mkellsy/rpi-case-model/CULTS3D/RPI-1.PNG

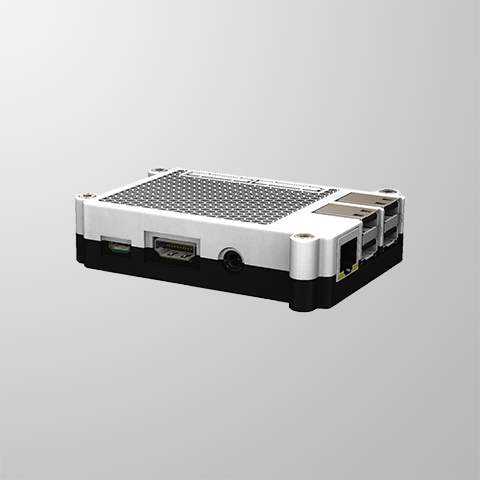
CULTS3D/RPI-1.PNG
