mkellsy/rpi-case-model/CULTS3D/RPI-2.PNG

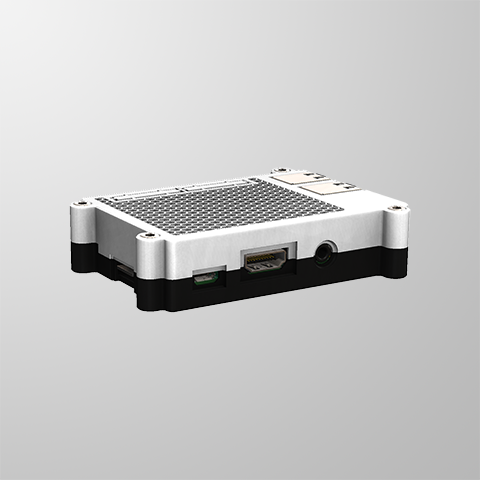
CULTS3D/RPI-2.PNG
