mkellsy/rpi-case-model/CULTS3D/RPI-3.PNG

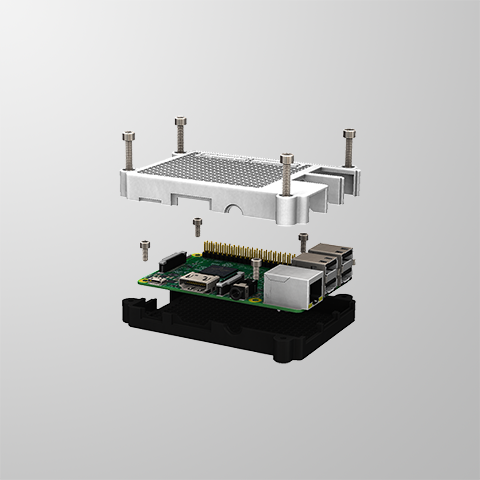
CULTS3D/RPI-3.PNG
