mkellsy/rpi-case-model/CULTS3D/RPI-4.PNG

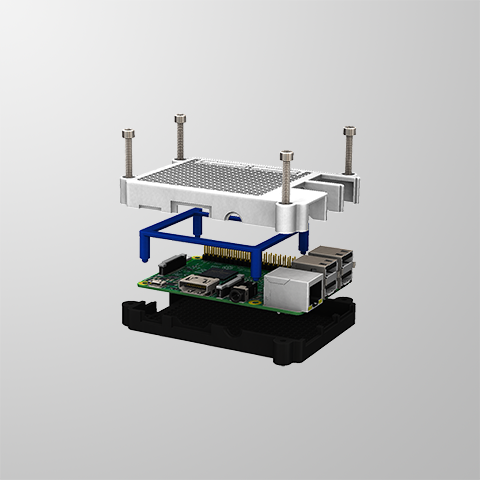
CULTS3D/RPI-4.PNG
