mkellsy/rpi-case-model/CULTS3D/RPI-5.PNG

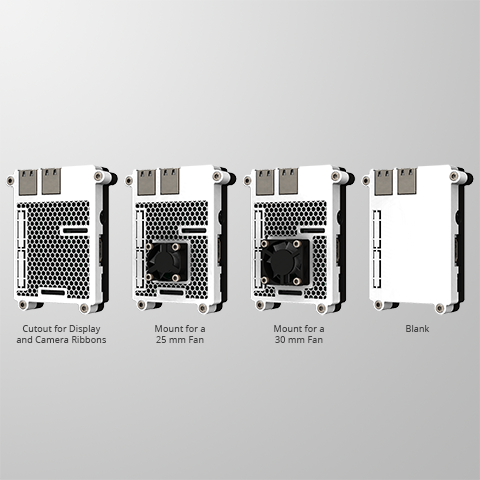
CULTS3D/RPI-5.PNG
