mkellsy/rpi-case-model/CULTS3D/RPI-6.PNG

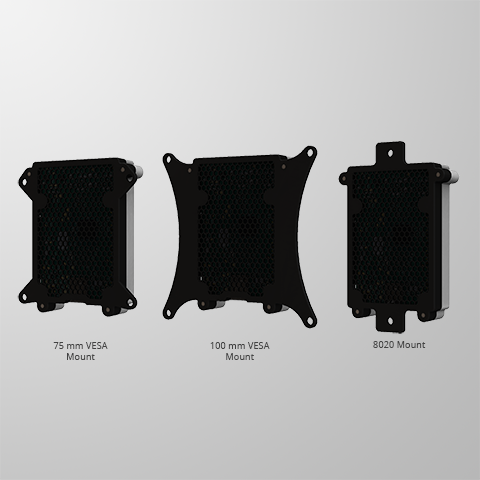
CULTS3D/RPI-6.PNG
