mkellsy/rpi-case-model/CULTS3D/RTS-1.PNG

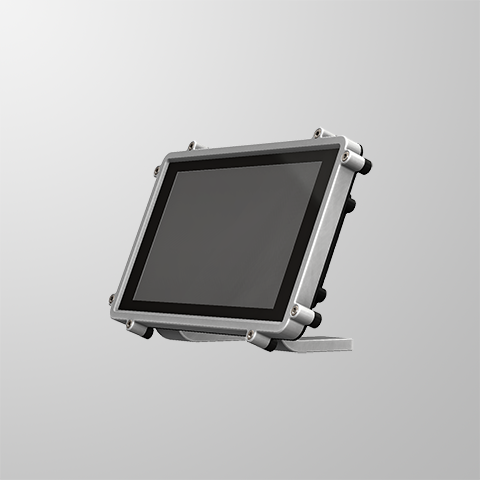
CULTS3D/RTS-1.PNG
