mkellsy/rpi-case-model/CULTS3D/RTS-2.PNG

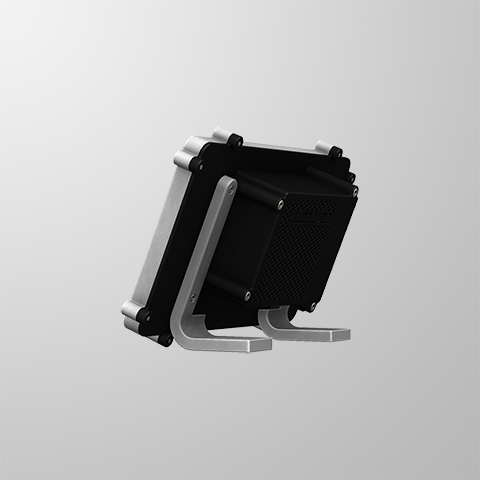
CULTS3D/RTS-2.PNG
