mkellsy/rpi-case-model/CULTS3D/RTS-3.PNG

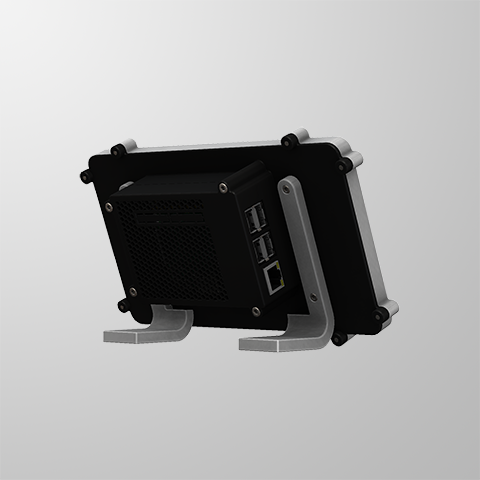
CULTS3D/RTS-3.PNG
