mkellsy/rpi-case-model/CULTS3D/RTS-4.PNG

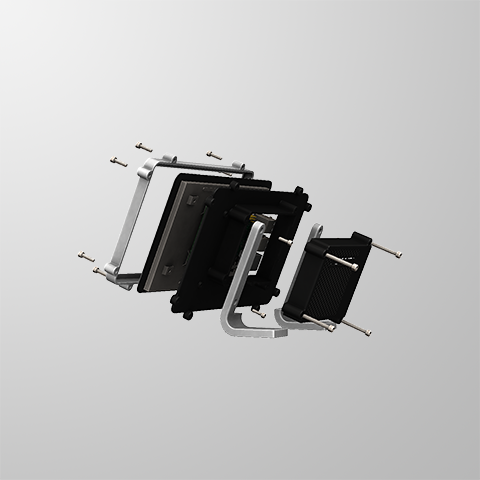
CULTS3D/RTS-4.PNG
