mkellsy/rpi-case-model/CULTS3D/RTS-5.PNG

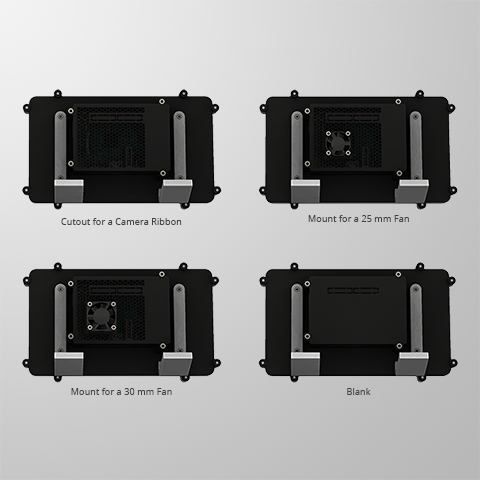
CULTS3D/RTS-5.PNG
