mkellsy/rpi-case-model/RENDERINGS/RPI3-1.JPG

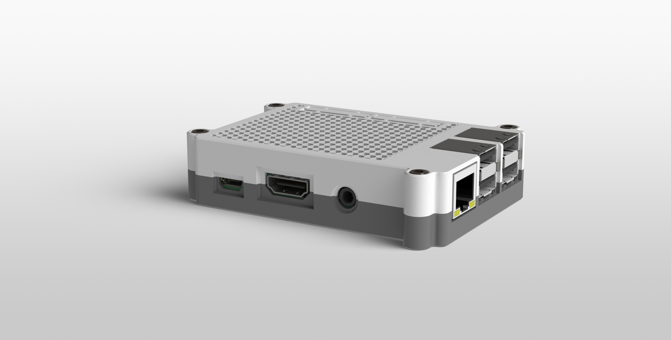
RENDERINGS/RPI3-1.JPG
