mkellsy/rpi-case-model/RENDERINGS/RPI3-2.JPG

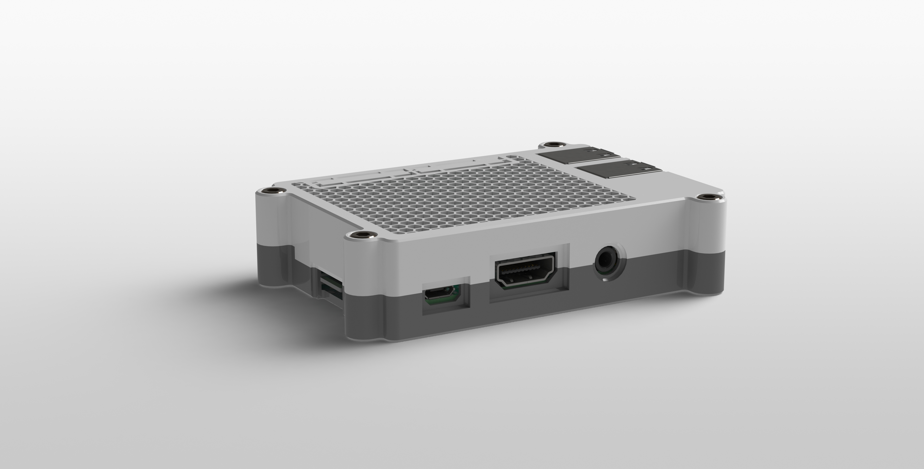
RENDERINGS/RPI3-2.JPG
