mkellsy/rpi-case-model/RENDERINGS/RPI3-3.JPG

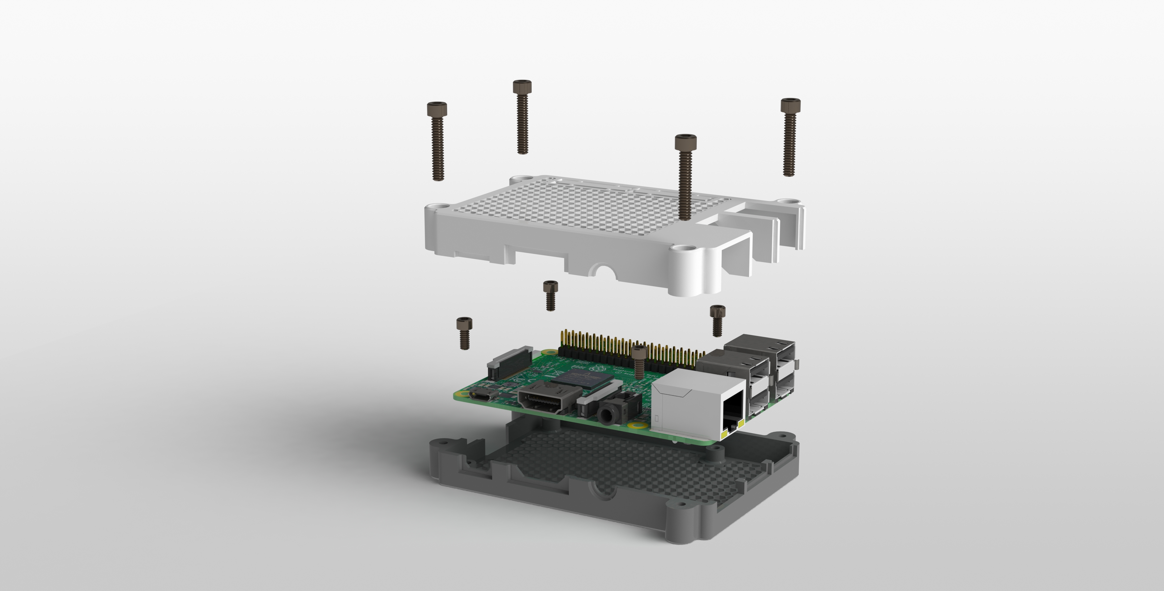
RENDERINGS/RPI3-3.JPG
