mkellsy/rpi-case-model/RENDERINGS/RPI3-5.JPG

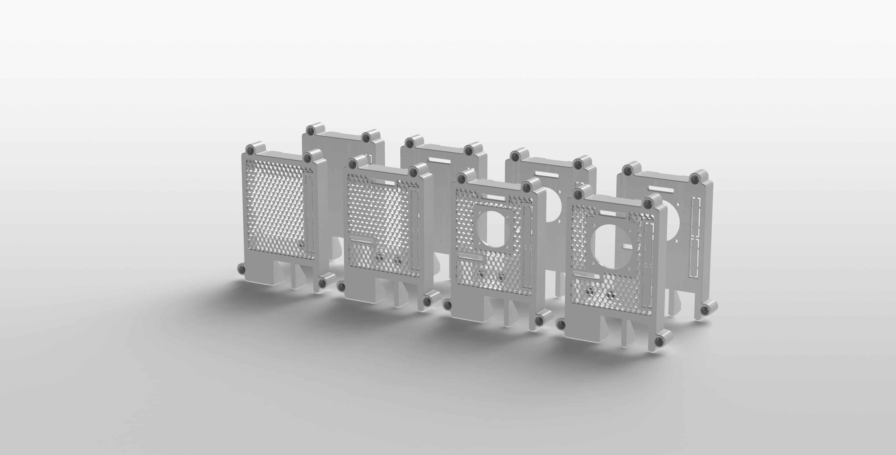
RENDERINGS/RPI3-5.JPG
