mkellsy/rpi-case-model/RENDERINGS/RPI3-6.JPG

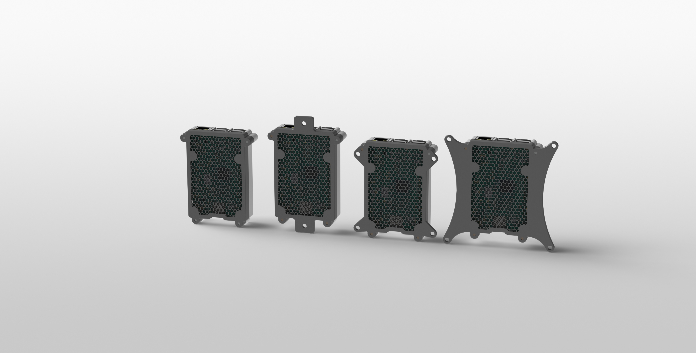
RENDERINGS/RPI3-6.JPG
