mkellsy/rpi-case-model/RENDERINGS/RPI4-1.JPG

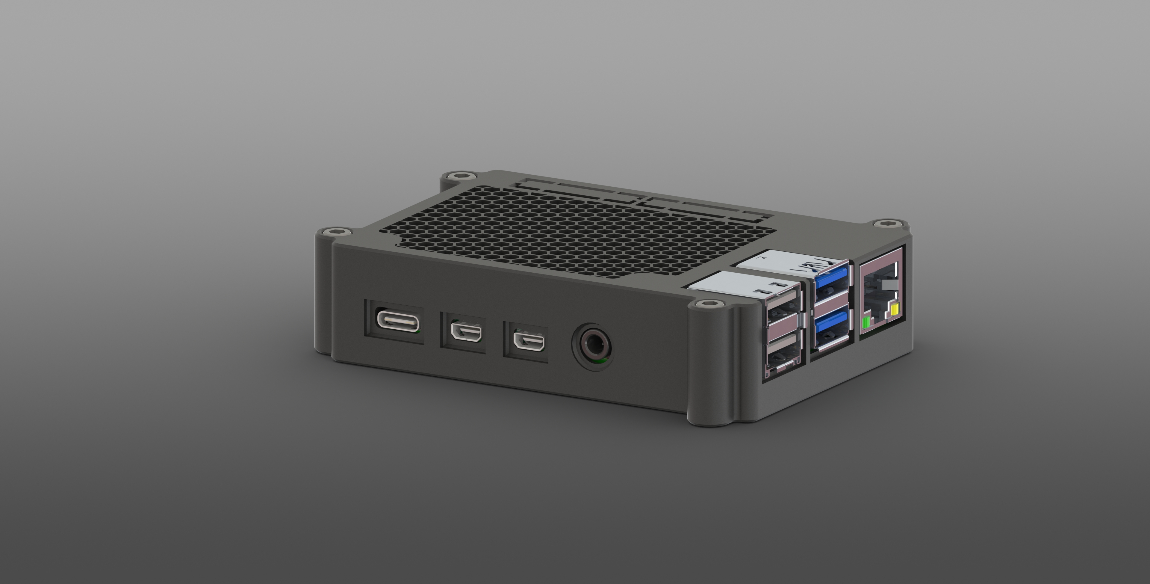
RENDERINGS/RPI4-1.JPG
