mkellsy/rpi-case-model/RENDERINGS/RPI4-2.JPG

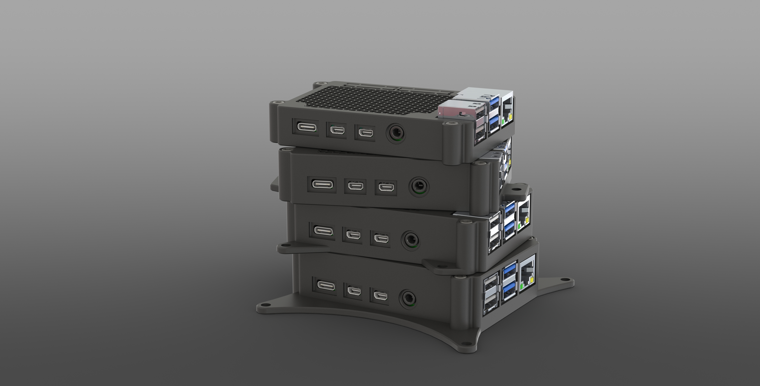
RENDERINGS/RPI4-2.JPG
