mkellsy/rpi-case-model/RENDERINGS/RPI4-3.JPG

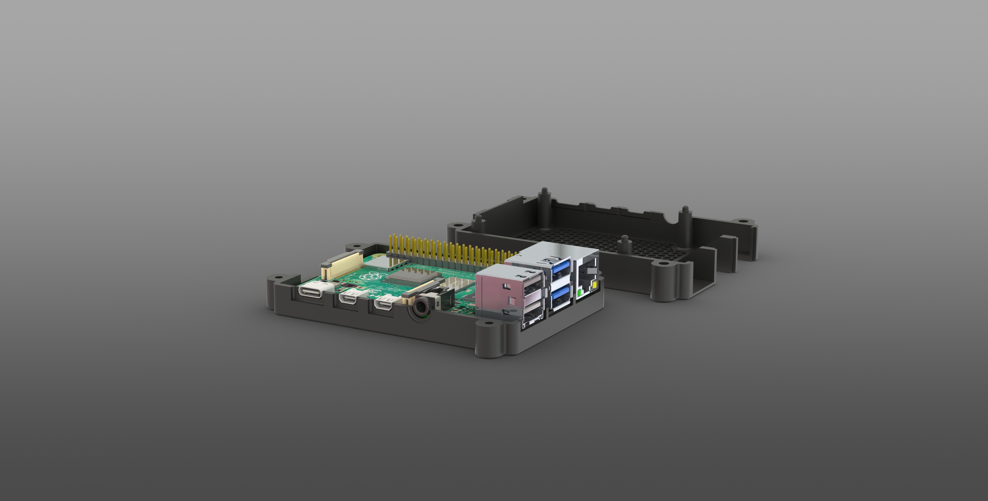
RENDERINGS/RPI4-3.JPG
