mkellsy/rpi-case-model/RENDERINGS/RPI4-4.JPG

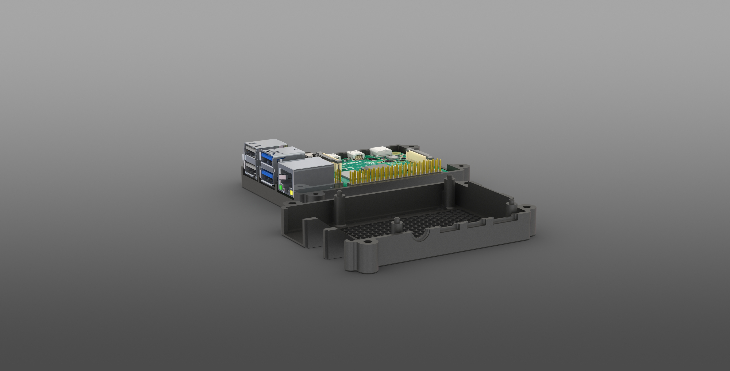
RENDERINGS/RPI4-4.JPG
