mkellsy/rpi-case-model/RENDERINGS/RPI4-5.JPG

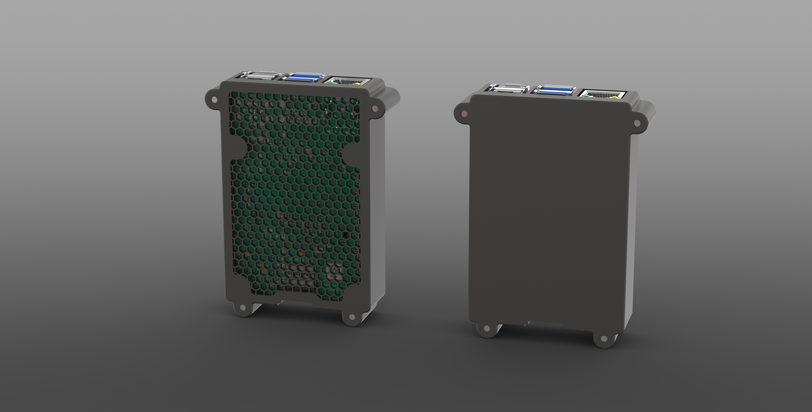
RENDERINGS/RPI4-5.JPG
