mkellsy/rpi-case-model/RENDERINGS/RPI4-6.JPG

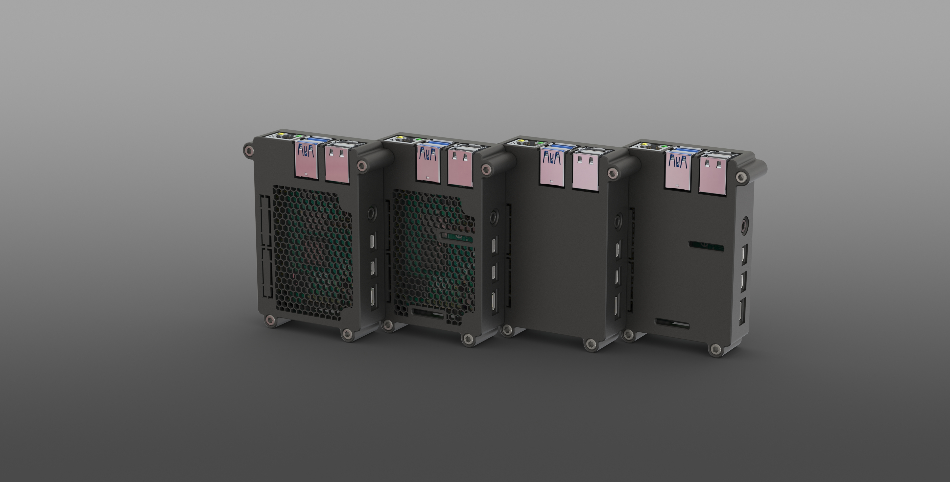
RENDERINGS/RPI4-6.JPG
