mkellsy/rpi-case-model/RENDERINGS/RPI4-7.JPG

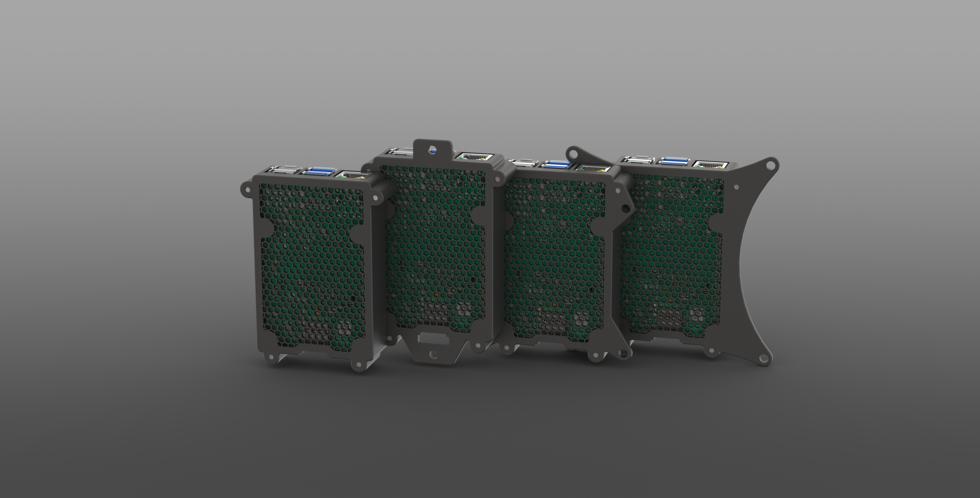
RENDERINGS/RPI4-7.JPG
