mkellsy/rpi-case-model/RENDERINGS/RPI4-8.JPG

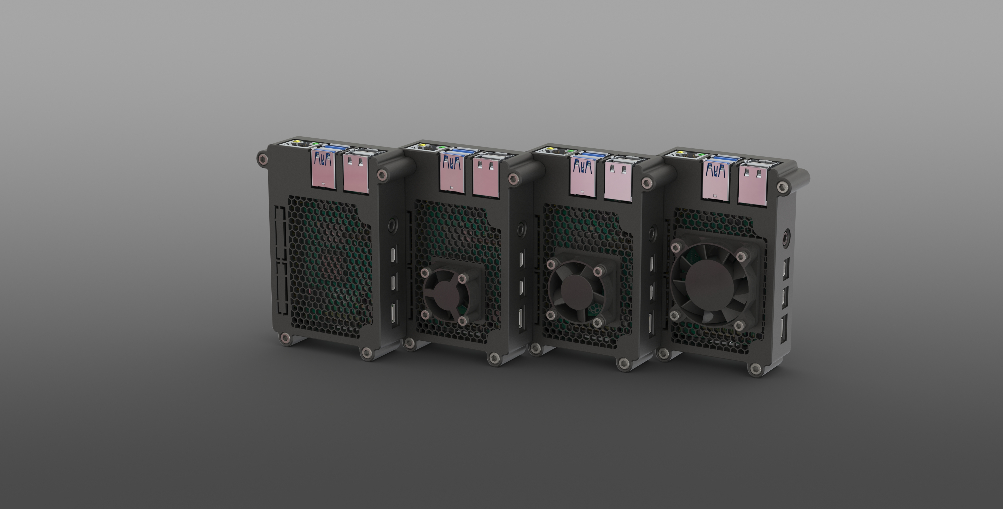
RENDERINGS/RPI4-8.JPG
