mkellsy/rpi-case-model/RENDERINGS/RTS3-1.JPG

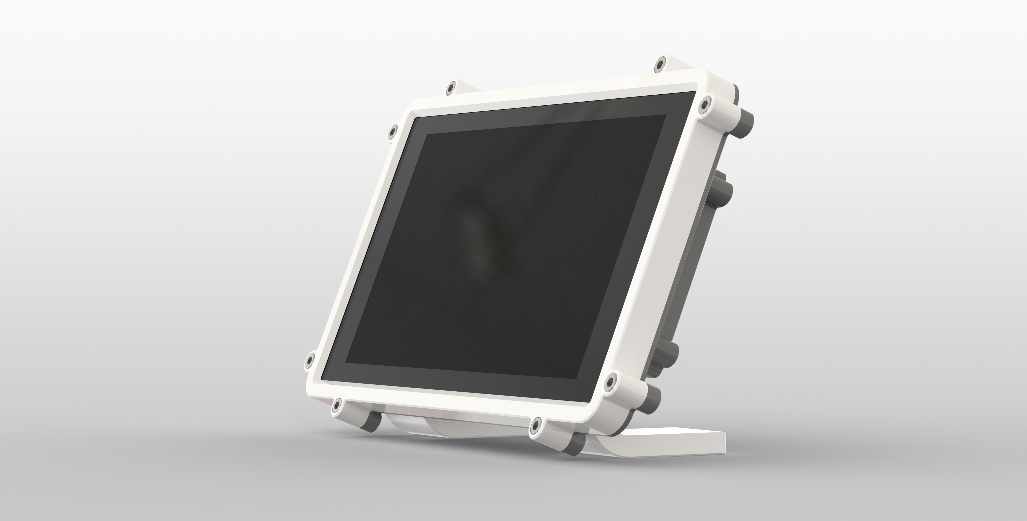
RENDERINGS/RTS3-1.JPG
