mkellsy/rpi-case-model/RENDERINGS/RTS3-2.JPG

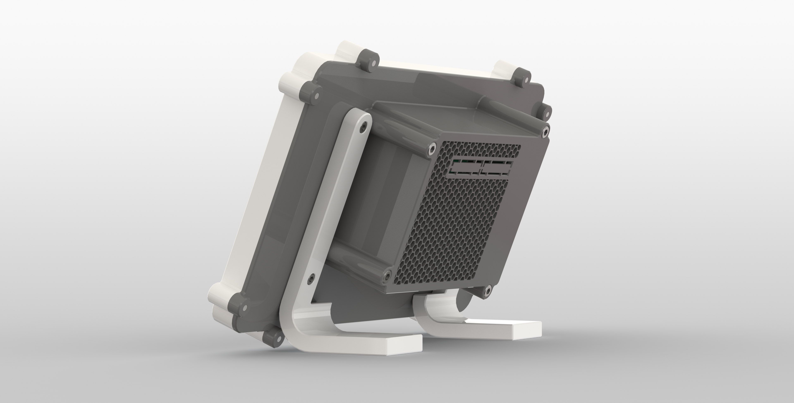
RENDERINGS/RTS3-2.JPG
