mkellsy/rpi-case-model/RENDERINGS/RTS3-3.JPG

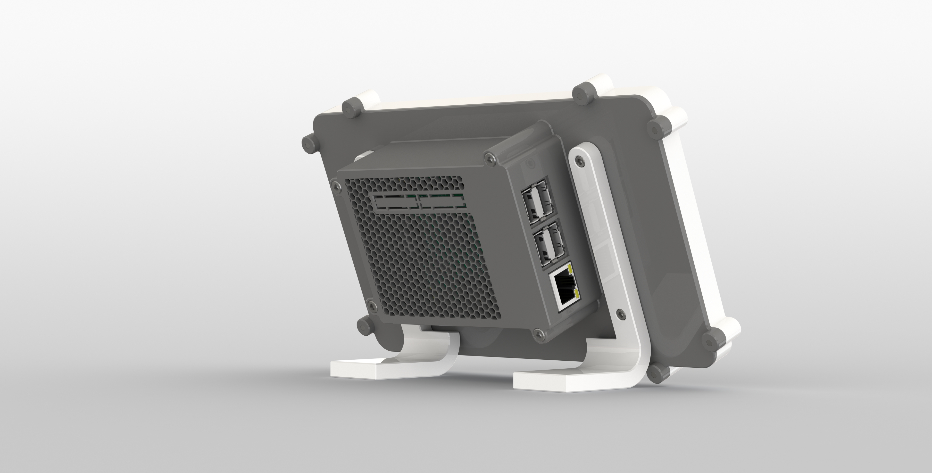
RENDERINGS/RTS3-3.JPG
