mkellsy/rpi-case-model/RENDERINGS/RTS3-4.JPG

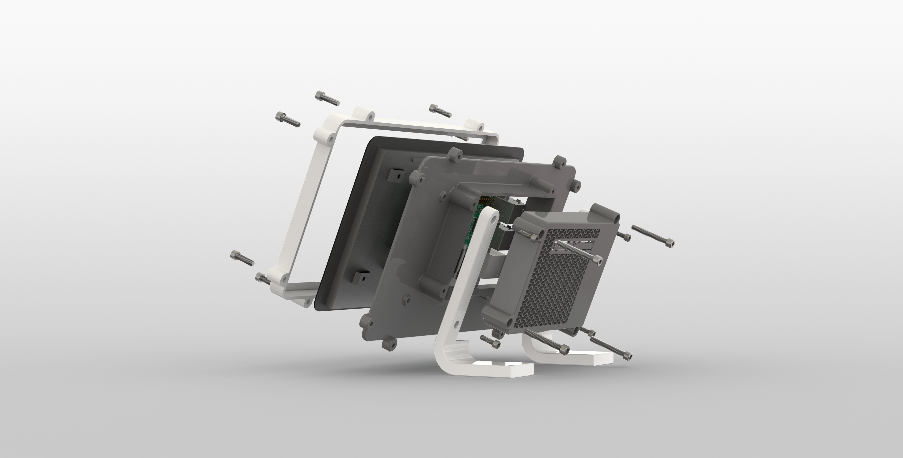
RENDERINGS/RTS3-4.JPG
