mkellsy/rpi-case-model/RENDERINGS/RTS3-5.JPG

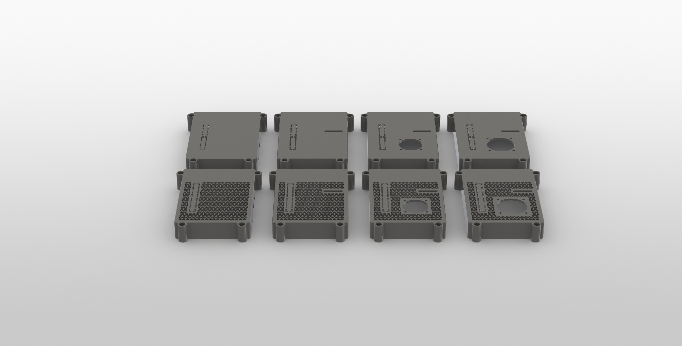
RENDERINGS/RTS3-5.JPG
