mkellsy/rpi-case-model/RENDERINGS/RTS4-1.JPG

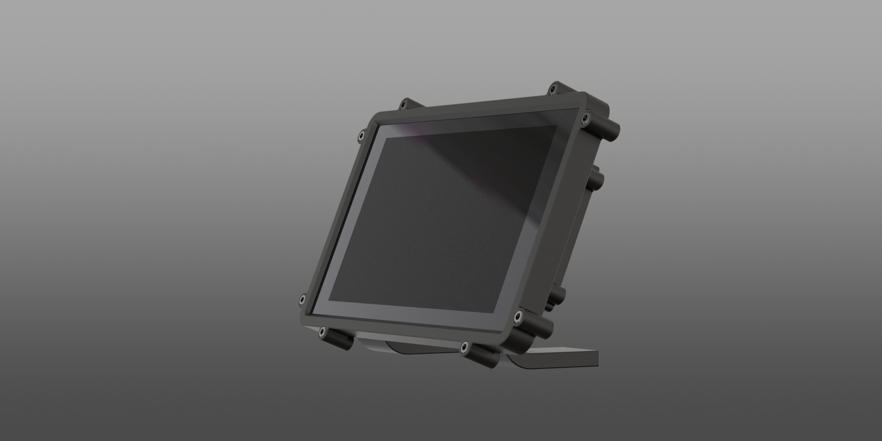
RENDERINGS/RTS4-1.JPG
