mkellsy/rpi-case-model/RENDERINGS/RTS4-2.JPG

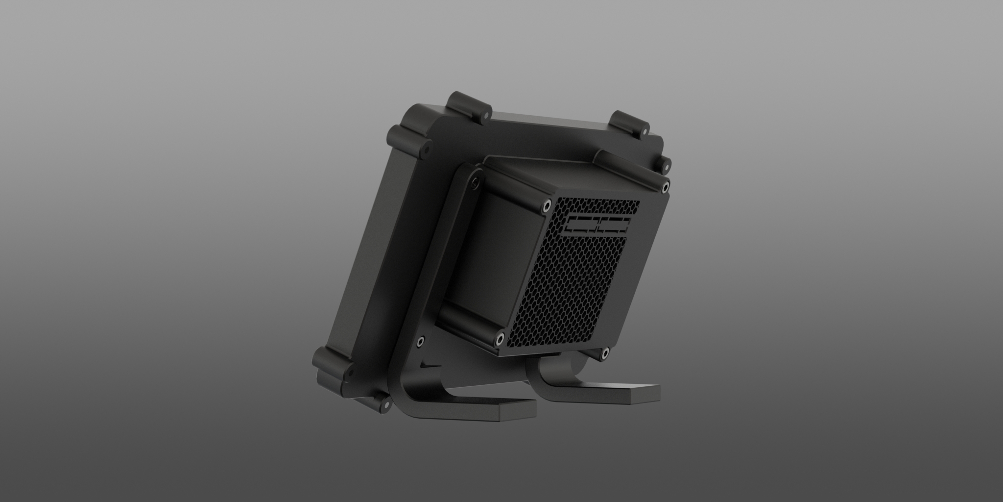
RENDERINGS/RTS4-2.JPG
