mkellsy/rpi-case-model/RENDERINGS/RTS4-3.JPG

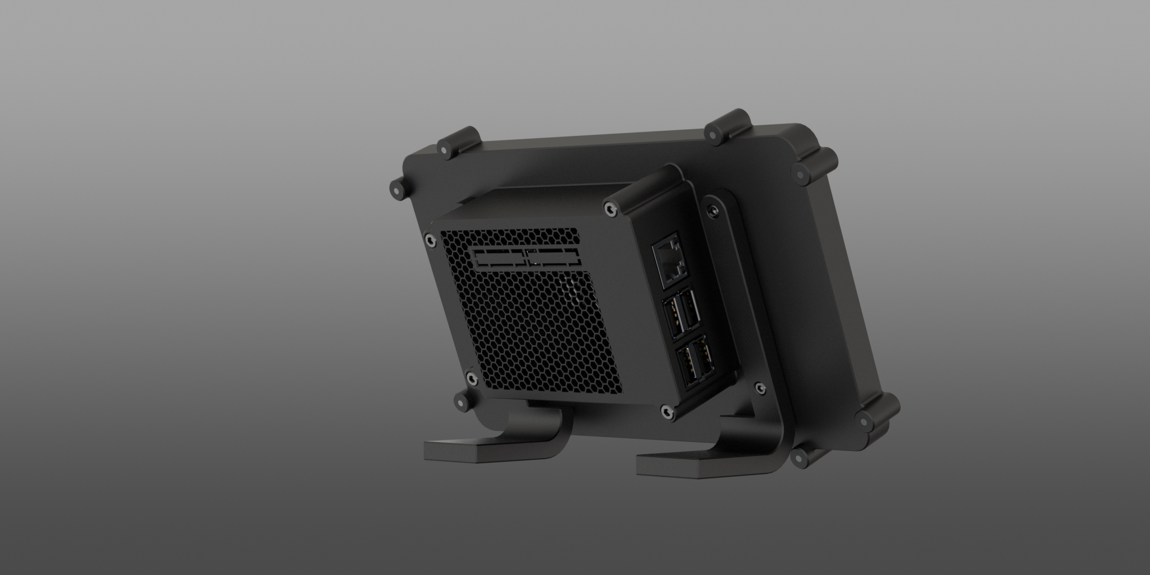
RENDERINGS/RTS4-3.JPG
