mkellsy/rpi-case-model/RENDERINGS/RTS4-4.JPG

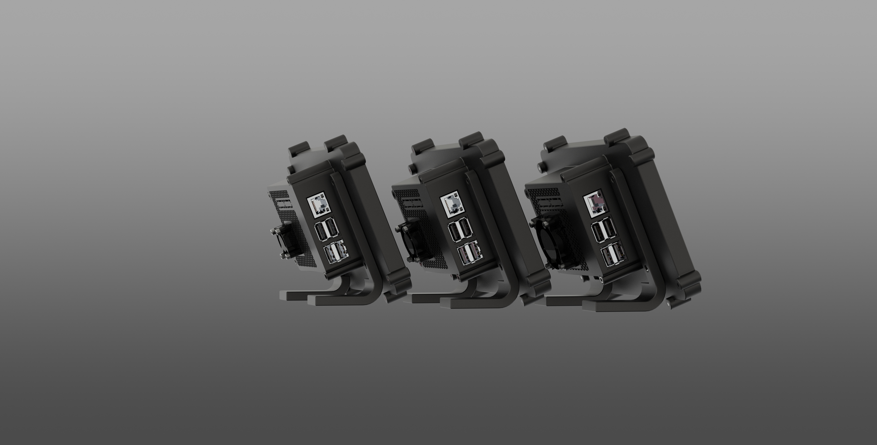
RENDERINGS/RTS4-4.JPG
