mkellsy/rpi-case-model/RENDERINGS/RTS4-5.JPG

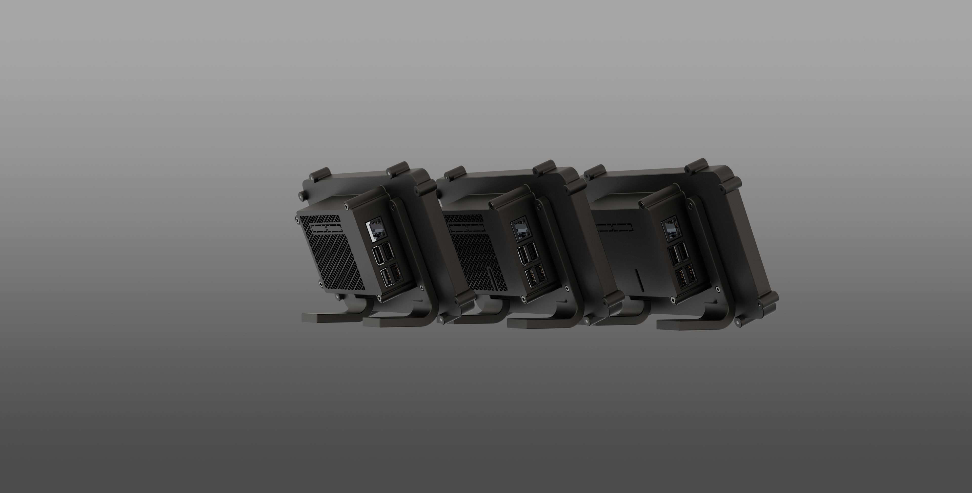
RENDERINGS/RTS4-5.JPG
