mkellsy/rpi-case-model/RENDERINGS/RWS4-2.JPG

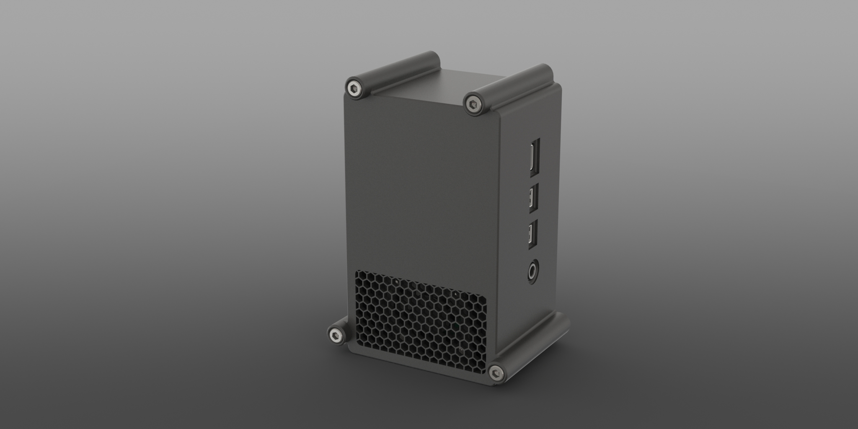
RENDERINGS/RWS4-2.JPG
