mkellsy/rpi-case-model/RENDERINGS/RWS4-3.JPG

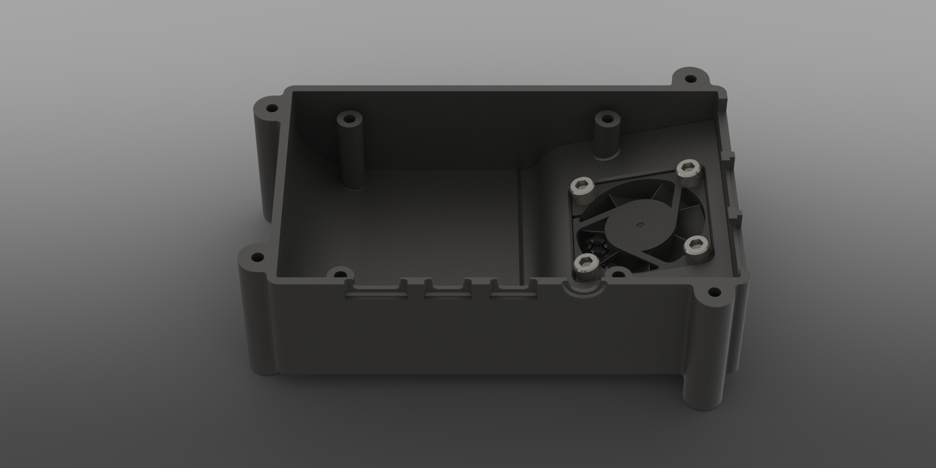
RENDERINGS/RWS4-3.JPG
