mkellsy/rpi-case-model/RENDERINGS/RWS4-4.JPG

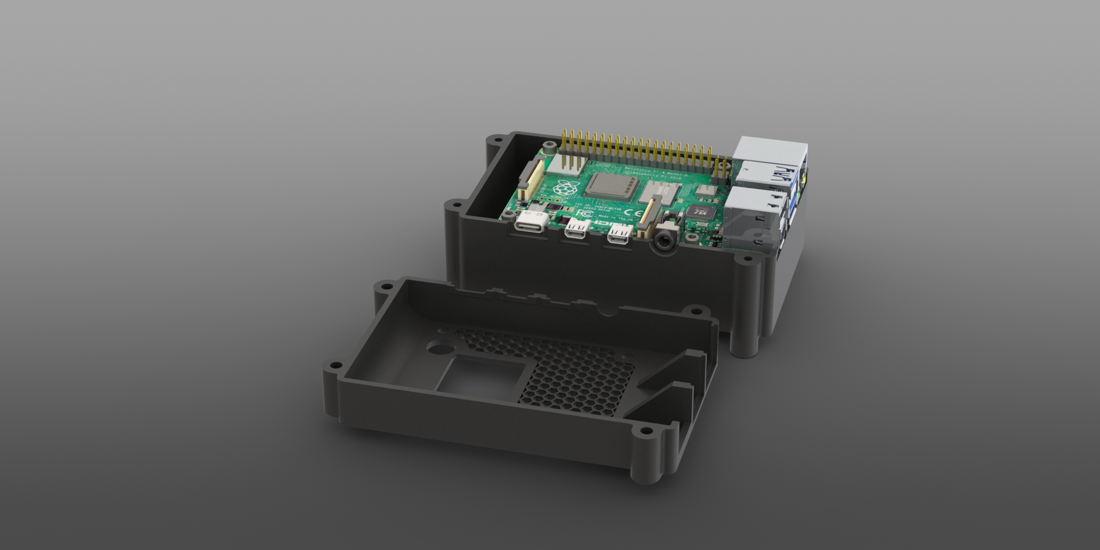
RENDERINGS/RWS4-4.JPG
