mkellsy/rpi-case-model/RENDERINGS/RWS4-5.JPG

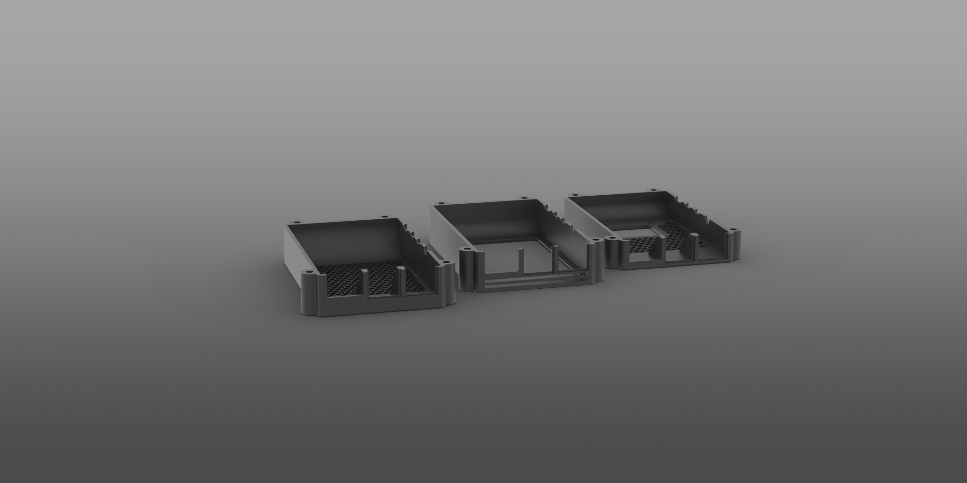
RENDERINGS/RWS4-5.JPG
