mkellsy/rpi-case-model/RENDERINGS/RWS4-6.JPG

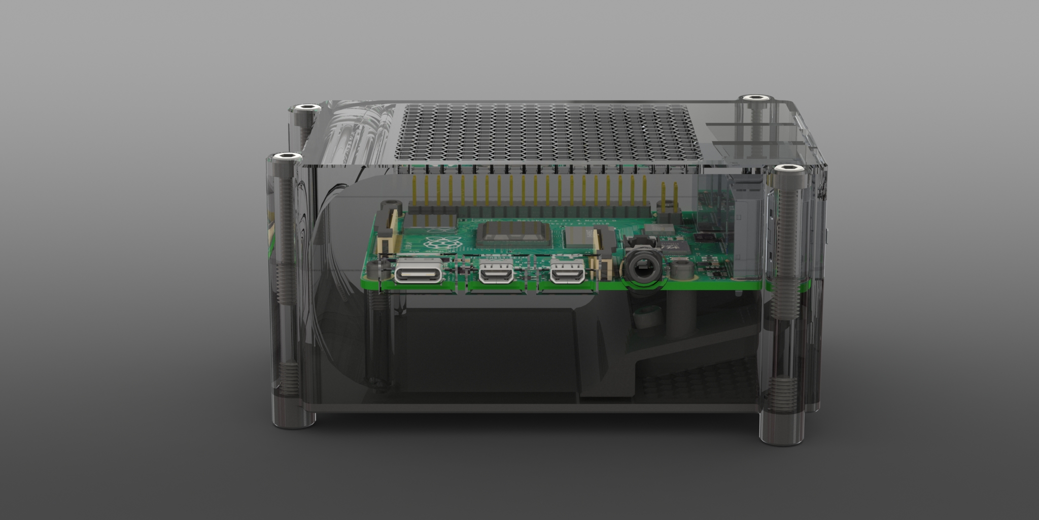
RENDERINGS/RWS4-6.JPG
