mkellsy/rpi-case-model/RPI4B/TOUCHSCREEN/Decal Back.png

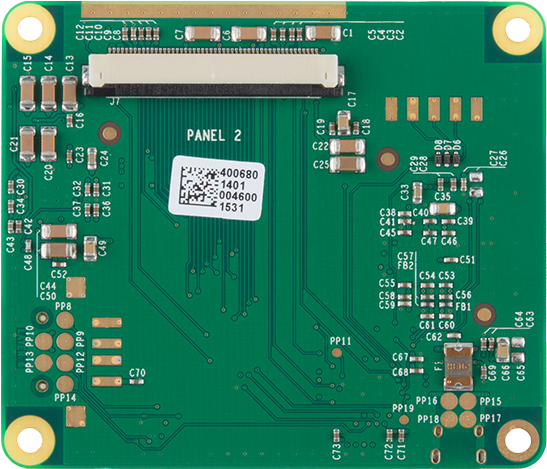
RPI4B/TOUCHSCREEN/Decal Back.png
