mkellsy/rpi-case-model/RPI4B/TOUCHSCREEN/Decal Front.png

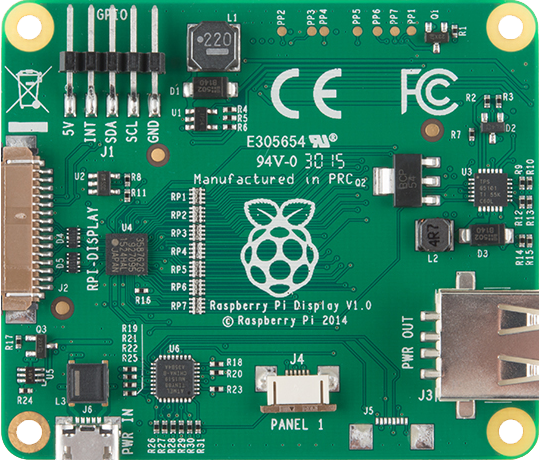
RPI4B/TOUCHSCREEN/Decal Front.png
