mkellsy/rpi-case-model/THINGVERSE/RPI3-1.PNG

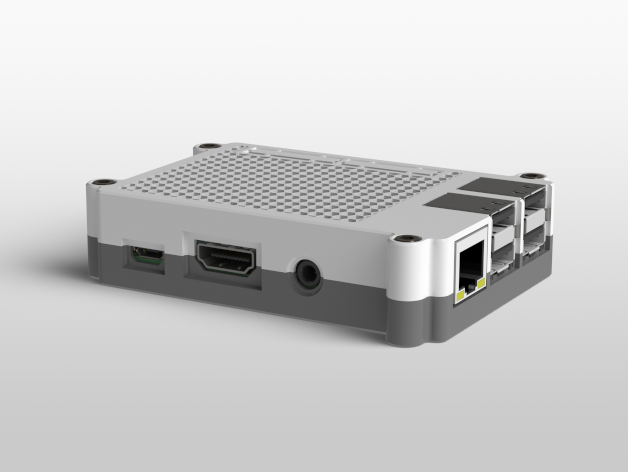
THINGVERSE/RPI3-1.PNG
