mkellsy/rpi-case-model/THINGVERSE/RPI3-2.PNG

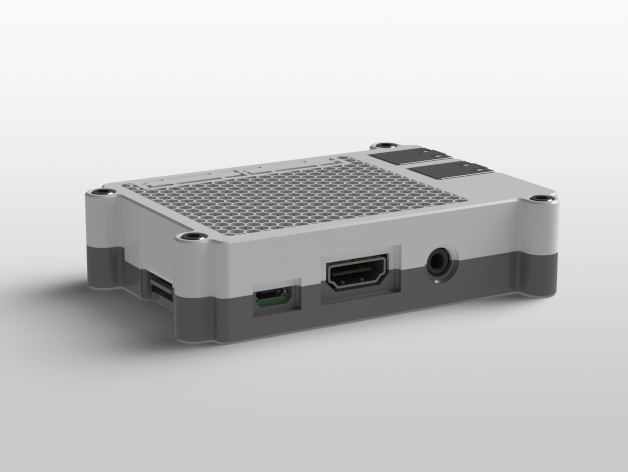
THINGVERSE/RPI3-2.PNG
