mkellsy/rpi-case-model/THINGVERSE/RPI3-3.PNG

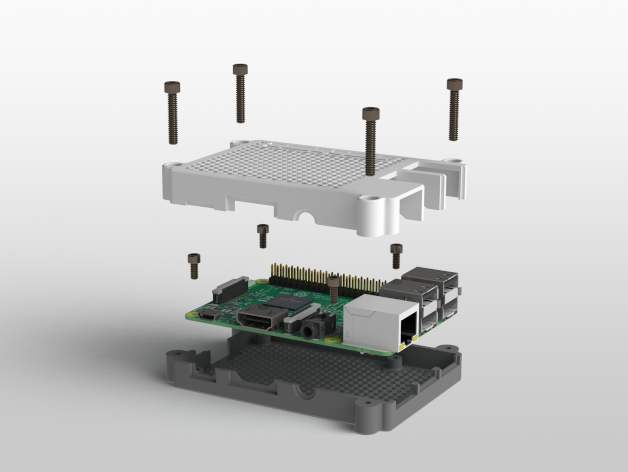
THINGVERSE/RPI3-3.PNG
