mkellsy/rpi-case-model/THINGVERSE/RPI3-5.PNG

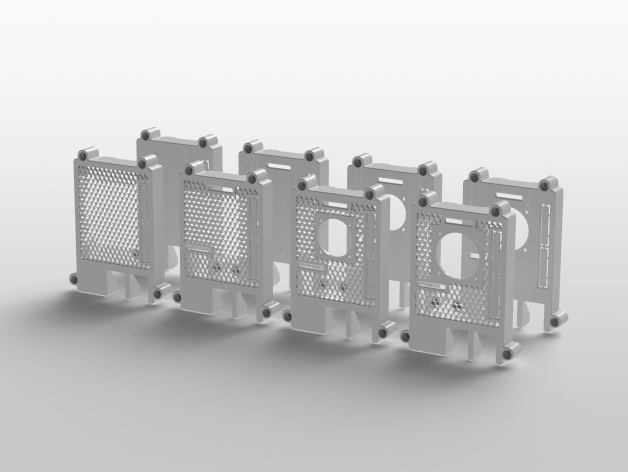
THINGVERSE/RPI3-5.PNG
