mkellsy/rpi-case-model/THINGVERSE/RPI3-6.PNG

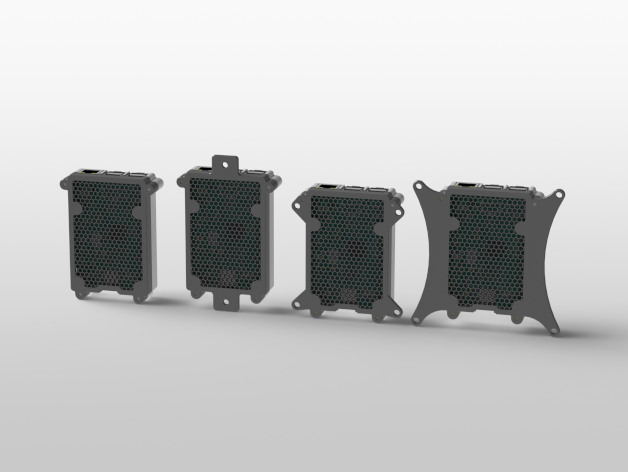
THINGVERSE/RPI3-6.PNG
