mkellsy/rpi-case-model/THINGVERSE/RPI4-2.png

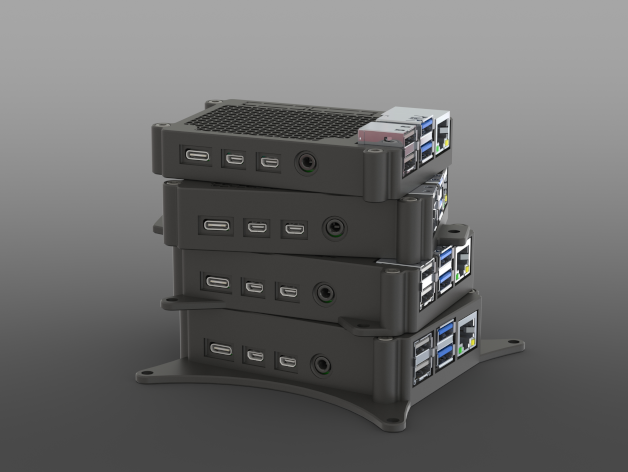
THINGVERSE/RPI4-2.png
