mkellsy/rpi-case-model/THINGVERSE/RPI4-3.png

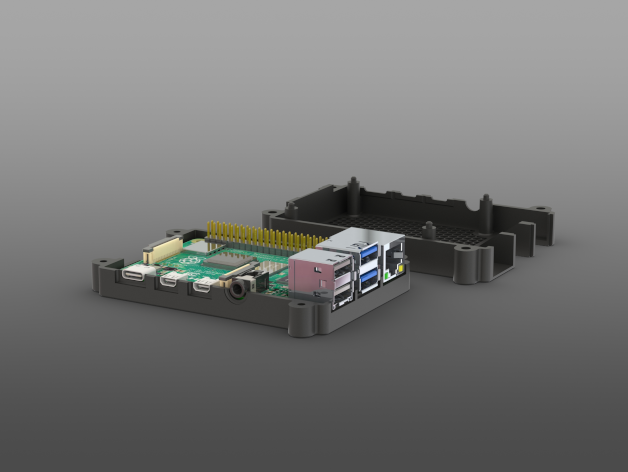
THINGVERSE/RPI4-3.png
