mkellsy/rpi-case-model/THINGVERSE/RPI4-4.png

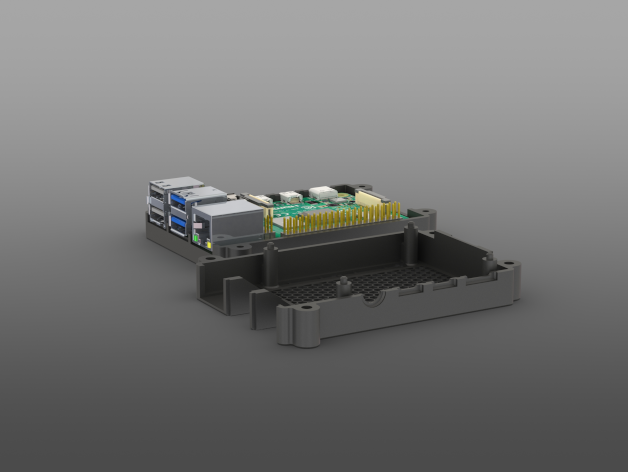
THINGVERSE/RPI4-4.png
