mkellsy/rpi-case-model/THINGVERSE/RPI4-5.png

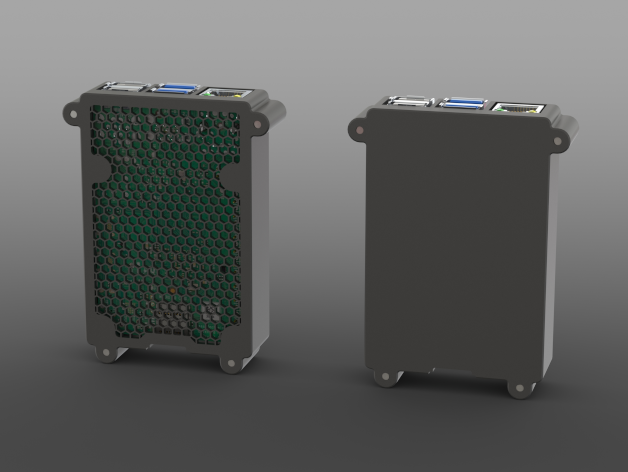
THINGVERSE/RPI4-5.png
