mkellsy/rpi-case-model/THINGVERSE/RPI4-6.png

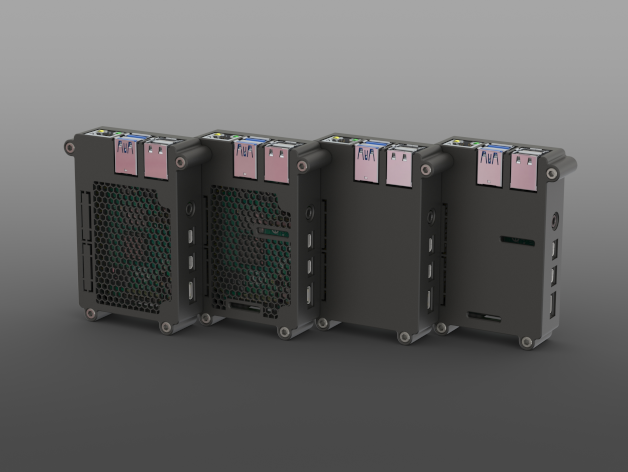
THINGVERSE/RPI4-6.png
