mkellsy/rpi-case-model/THINGVERSE/RPI4-7.png

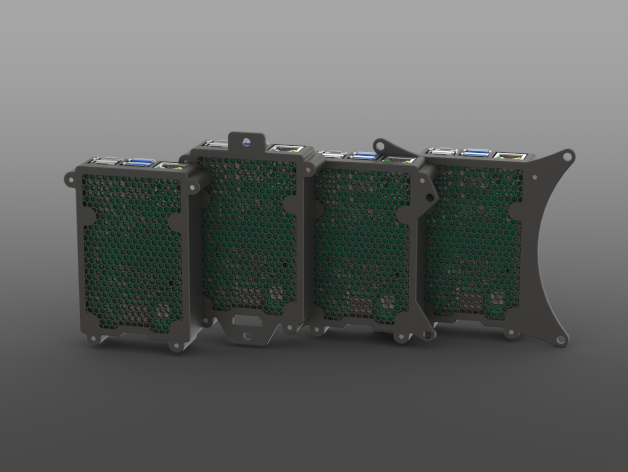
THINGVERSE/RPI4-7.png
