mkellsy/rpi-case-model/THINGVERSE/RPI4-8.png

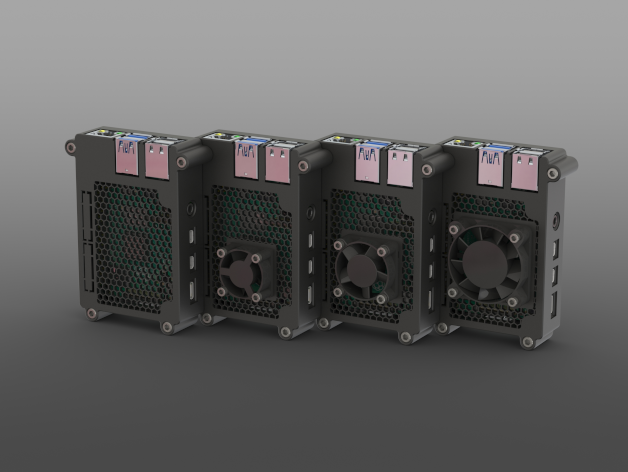
THINGVERSE/RPI4-8.png
