mkellsy/rpi-case-model/THINGVERSE/RTS3-1.PNG

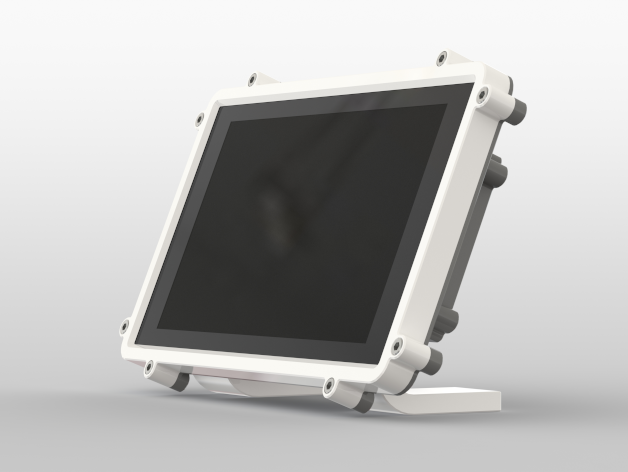
THINGVERSE/RTS3-1.PNG
