mkellsy/rpi-case-model/THINGVERSE/RTS3-2.PNG

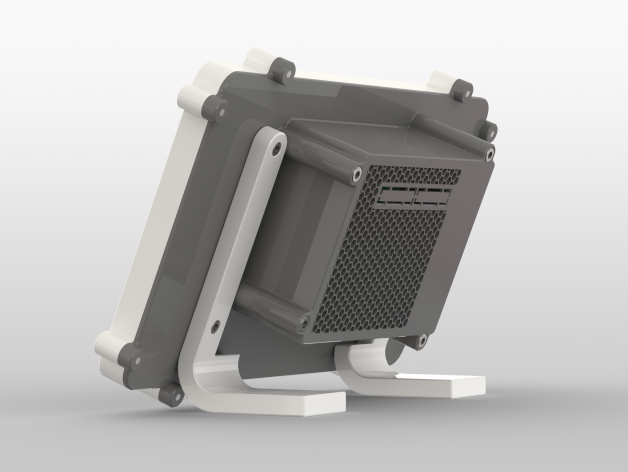
THINGVERSE/RTS3-2.PNG
