mkellsy/rpi-case-model/THINGVERSE/RTS3-3.PNG

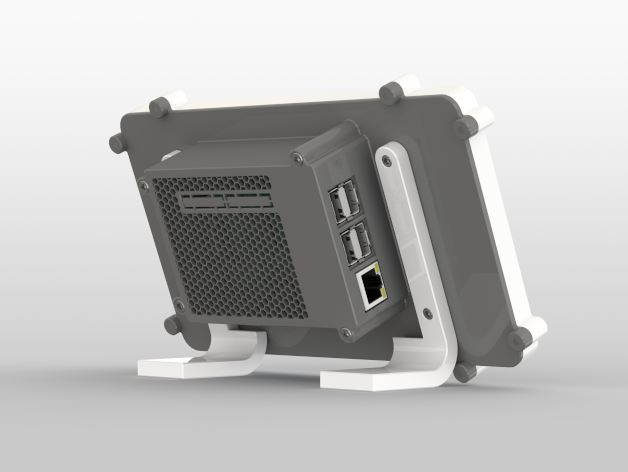
THINGVERSE/RTS3-3.PNG
