mkellsy/rpi-case-model/THINGVERSE/RTS3-4.PNG

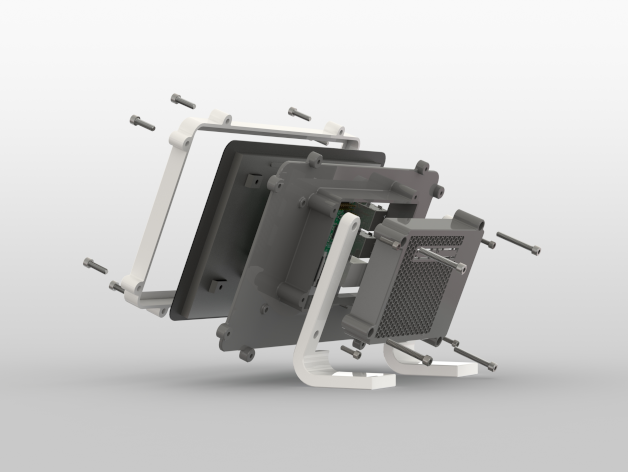
THINGVERSE/RTS3-4.PNG
