mkellsy/rpi-case-model/THINGVERSE/RTS3-5.PNG

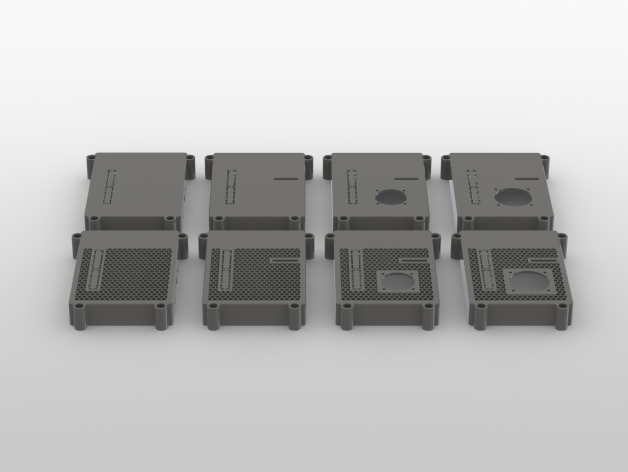
THINGVERSE/RTS3-5.PNG
