mkellsy/rpi-case-model/THINGVERSE/RTS4-1.PNG

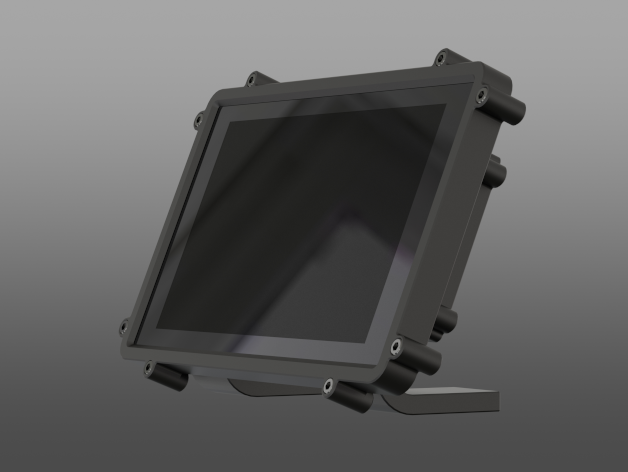
THINGVERSE/RTS4-1.PNG
