mkellsy/rpi-case-model/THINGVERSE/RTS4-2.PNG

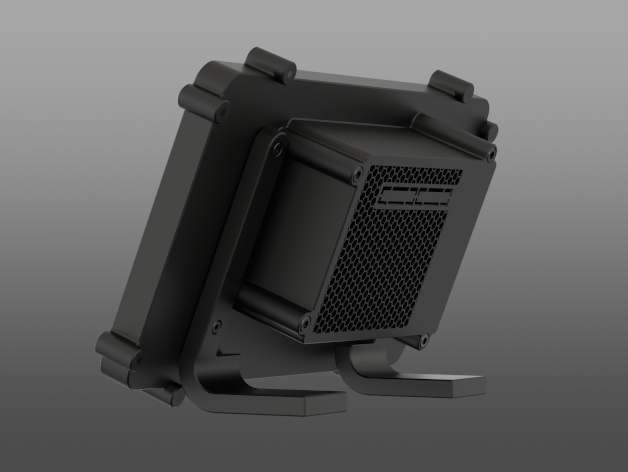
THINGVERSE/RTS4-2.PNG
