mkellsy/rpi-case-model/THINGVERSE/RTS4-3.PNG

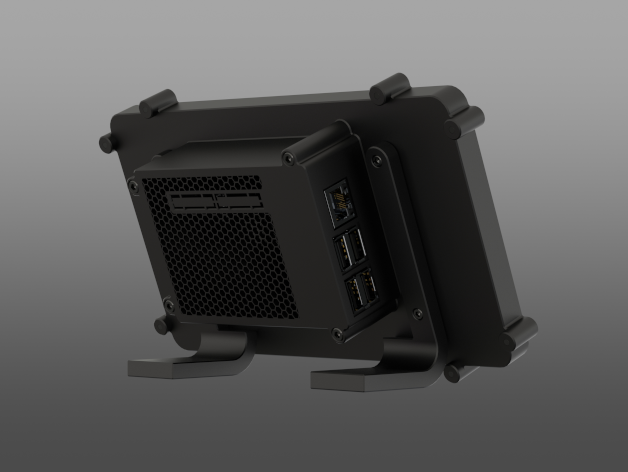
THINGVERSE/RTS4-3.PNG
