mkellsy/rpi-case-model/THINGVERSE/RTS4-4.PNG

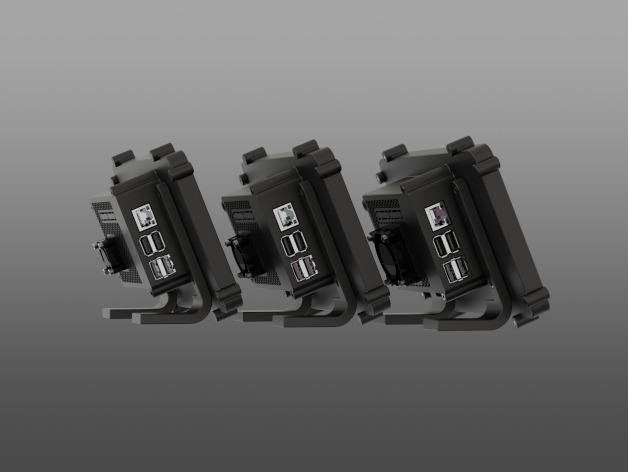
THINGVERSE/RTS4-4.PNG
