mkellsy/rpi-case-model/THINGVERSE/RTS4-5.PNG

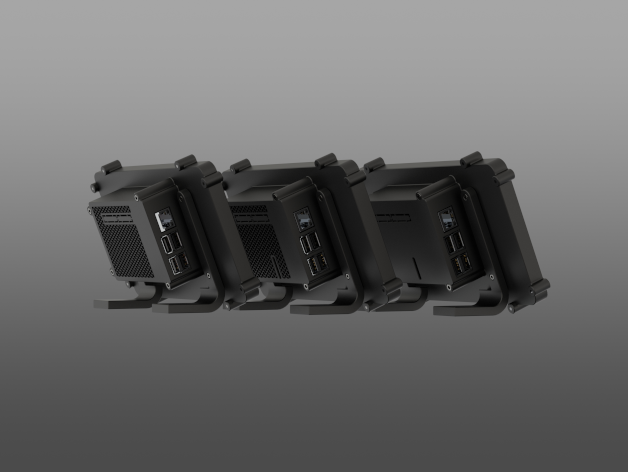
THINGVERSE/RTS4-5.PNG
