mkellsy/rpi-case-model/THINGVERSE/RWS4-1.PNG

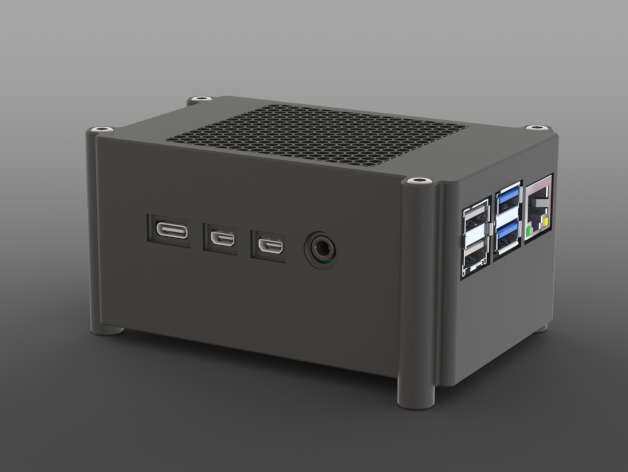
THINGVERSE/RWS4-1.PNG
