mkellsy/rpi-case-model/THINGVERSE/RWS4-2.PNG

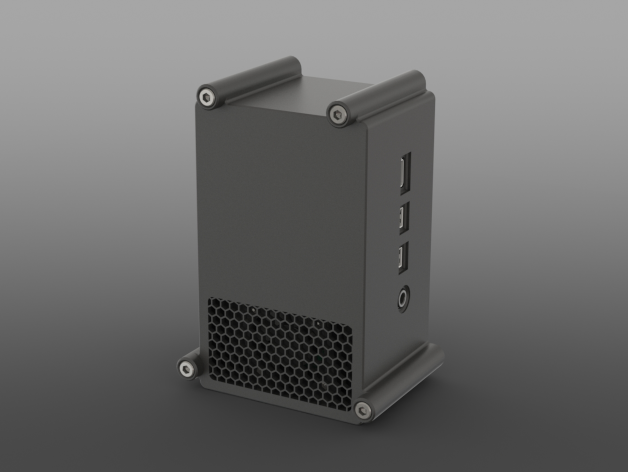
THINGVERSE/RWS4-2.PNG
