mkellsy/rpi-case-model/THINGVERSE/RWS4-3.PNG

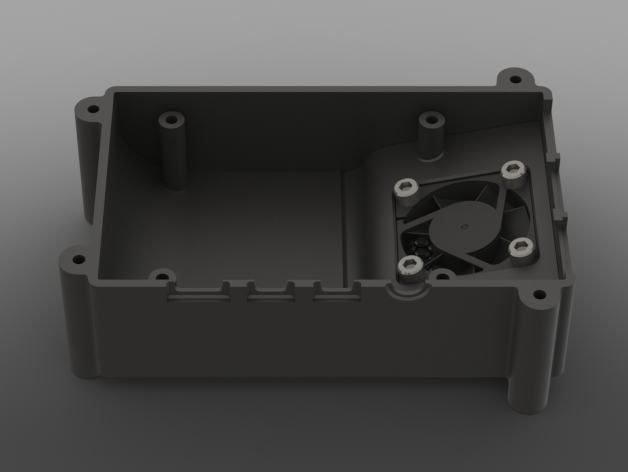
THINGVERSE/RWS4-3.PNG
