mkellsy/rpi-case-model/THINGVERSE/RWS4-4.PNG

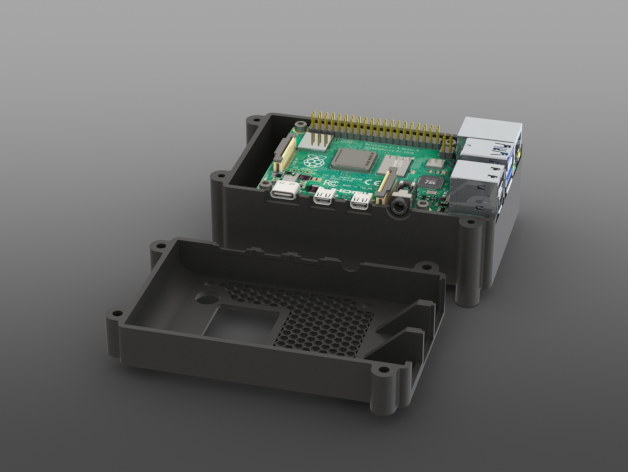
THINGVERSE/RWS4-4.PNG
