mkellsy/rpi-case-model/THINGVERSE/RWS4-5.PNG

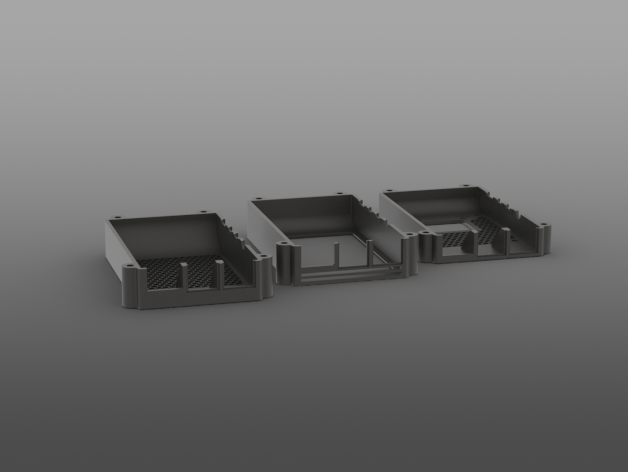
THINGVERSE/RWS4-5.PNG
