mkellsy/rpi-case-model/THINGVERSE/RWS4-6.PNG

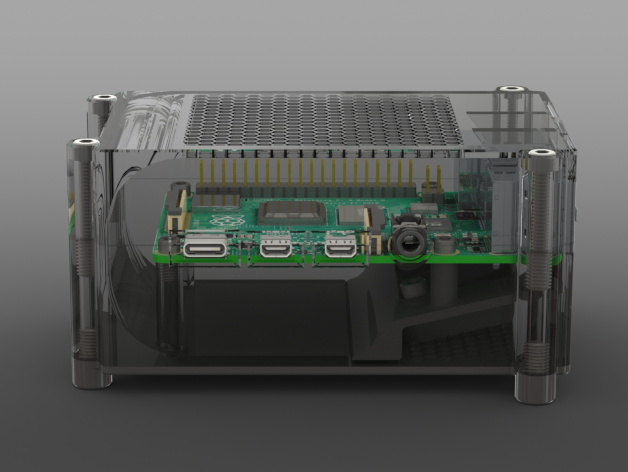
THINGVERSE/RWS4-6.PNG
