mkellsy/rpi-case-model/RPI4B/BOARD/Gigabit Ethernet Port, RPi4ModelB.SLDPRT

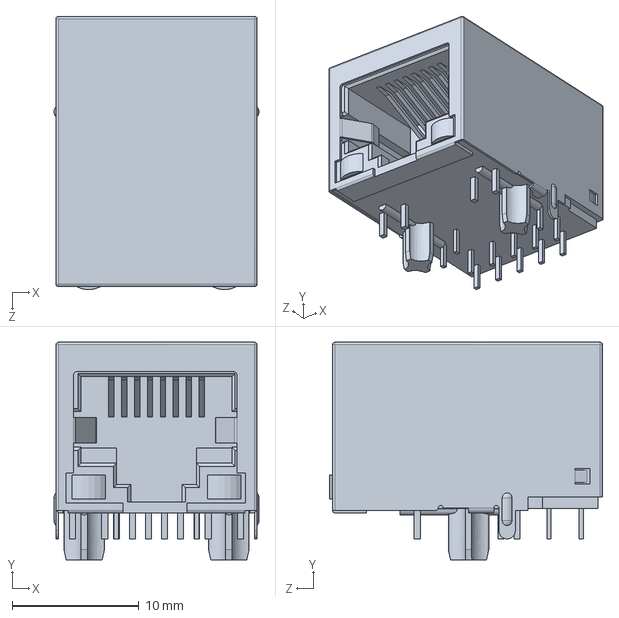
[picture p89: CAD file, 2020-10-01]
RPI4B/BOARD/Gigabit Ethernet Port, RPi4ModelB.SLDPRT
16.2 x 17.2 x 21.6 mm
