mkellsy/rpi-case-model/RPI4B/CASE/BEZEL.SLDPRT

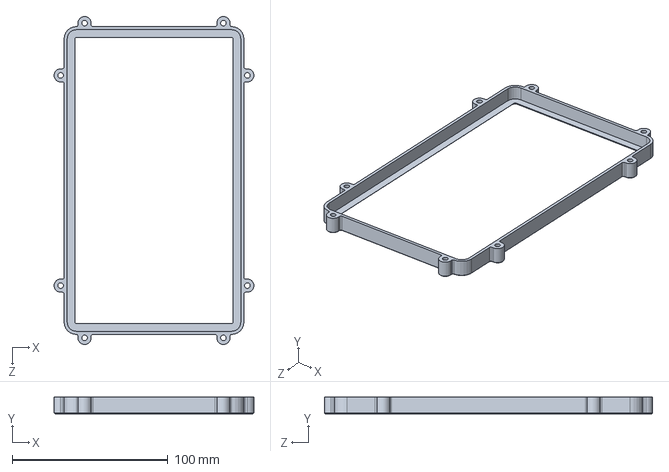
[picture p90: CAD file, 2020-10-23]
RPI4B/CASE/BEZEL.SLDPRT
128.3 x 10.6 x 210.5 mm
