mkellsy/rpi-case-model/RPI4B/COMPONENTS/HOUSING.SLDPRT

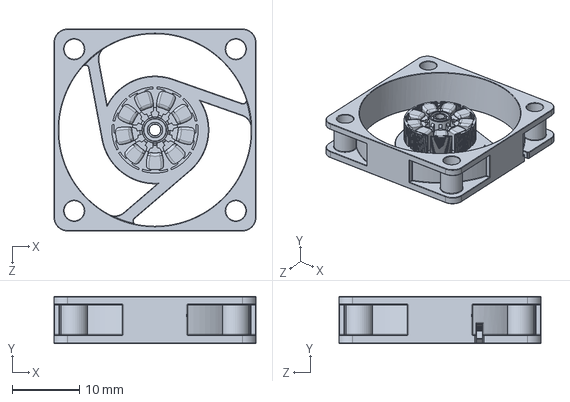
[picture p91: CAD file, 2020-10-01]
RPI4B/COMPONENTS/HOUSING.SLDPRT
30.0 x 7.00 x 30.0 mm
