mkellsy/rpi-case-model/RPI4B/PUBLISH/BLOWER/BAFFLE.STL

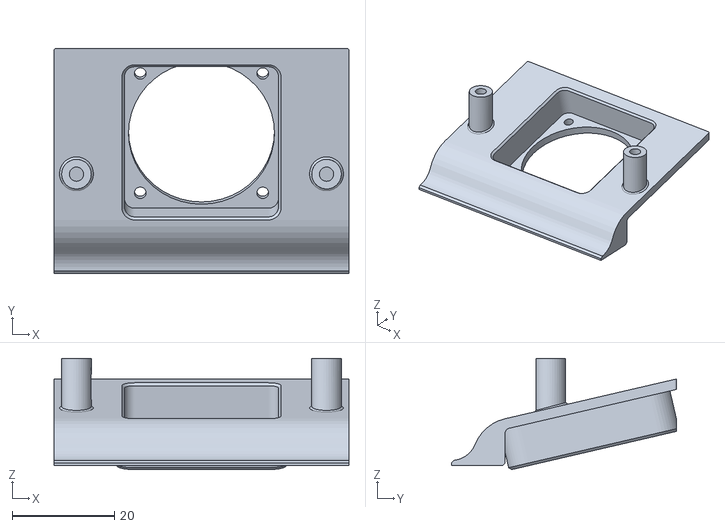
[picture p92: CAD file, 2020-10-01]
RPI4B/PUBLISH/BLOWER/BAFFLE.STL
57.8 x 44.1 x 21.8
