mkellsy/rpi-case-model/RPI4B/PUBLISH/GRILL_40MM.STL

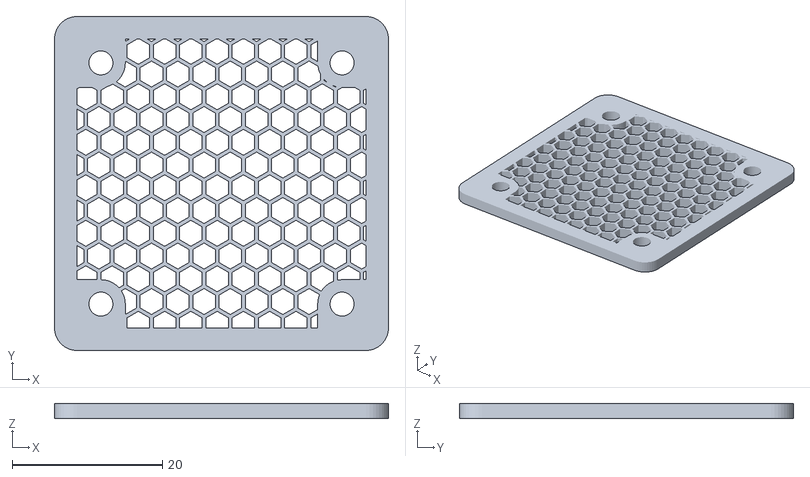
[picture p94: CAD file, 2019-08-16]
RPI4B/PUBLISH/GRILL_40MM.STL
44.5 x 44.5 x 2.00
