mkellsy/rpi-case-model/RPI4B/PUBLISH/SLIM/TOP_40MM.STL

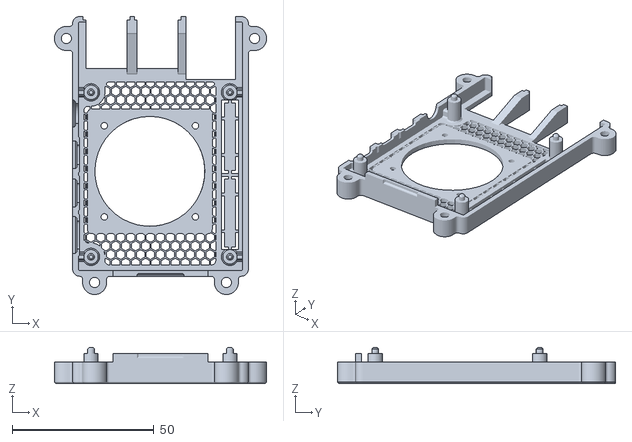
[picture p95: CAD file, 2019-08-11]
RPI4B/PUBLISH/SLIM/TOP_40MM.STL
74.9 x 98.0 x 12.7
