mkellsy/rpi-case-model/RPI4B/TOUCHSCREEN/FRONT-GLASS.SLDPRT

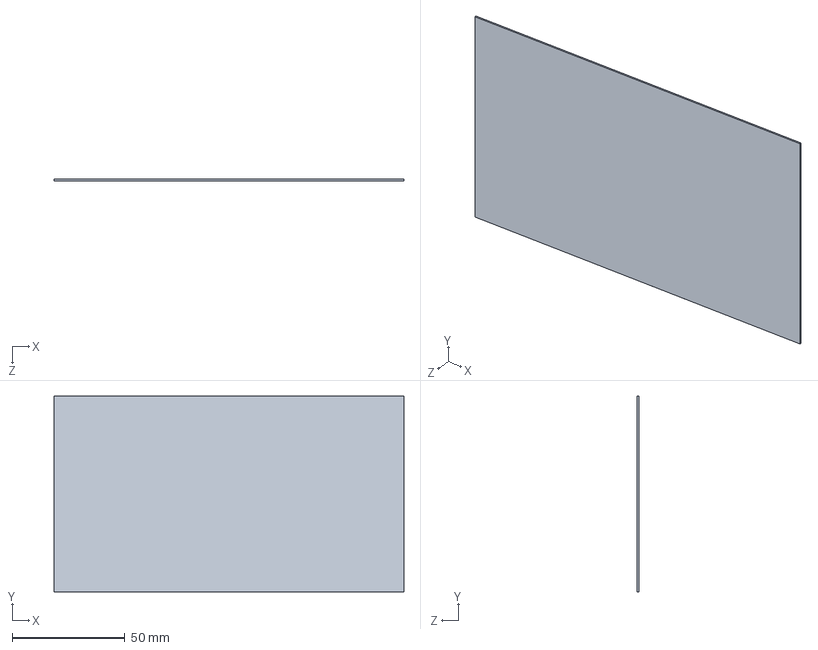
[picture p97: CAD file, 2020-09-30]
RPI4B/TOUCHSCREEN/FRONT-GLASS.SLDPRT
154.9 x 86.7 x 0.7 mm
