mkellsy/rpi-case-model/RPI4B/BLOWER/VENTED.SLDPRT

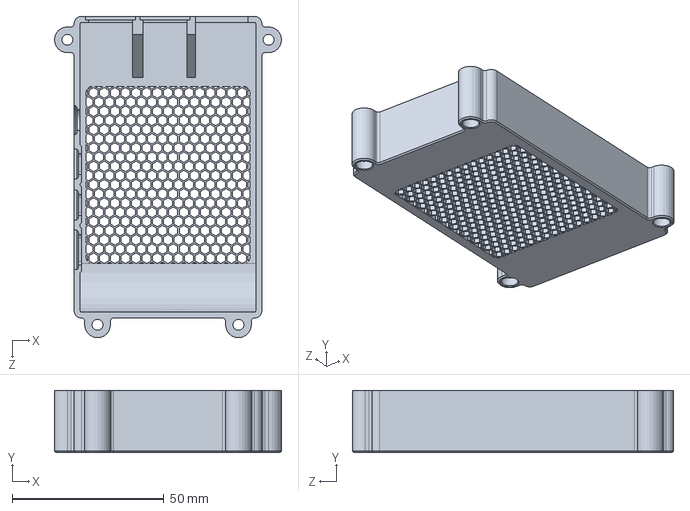
[picture p98: CAD file, 2020-10-01]
RPI4B/BLOWER/VENTED.SLDPRT
74.9 x 20.5 x 106.1 mm
