mkellsy/rpi-case-model/RPI4B/BOARD/2X USB2.0 PORTS, RPi4ModelB.SLDPRT

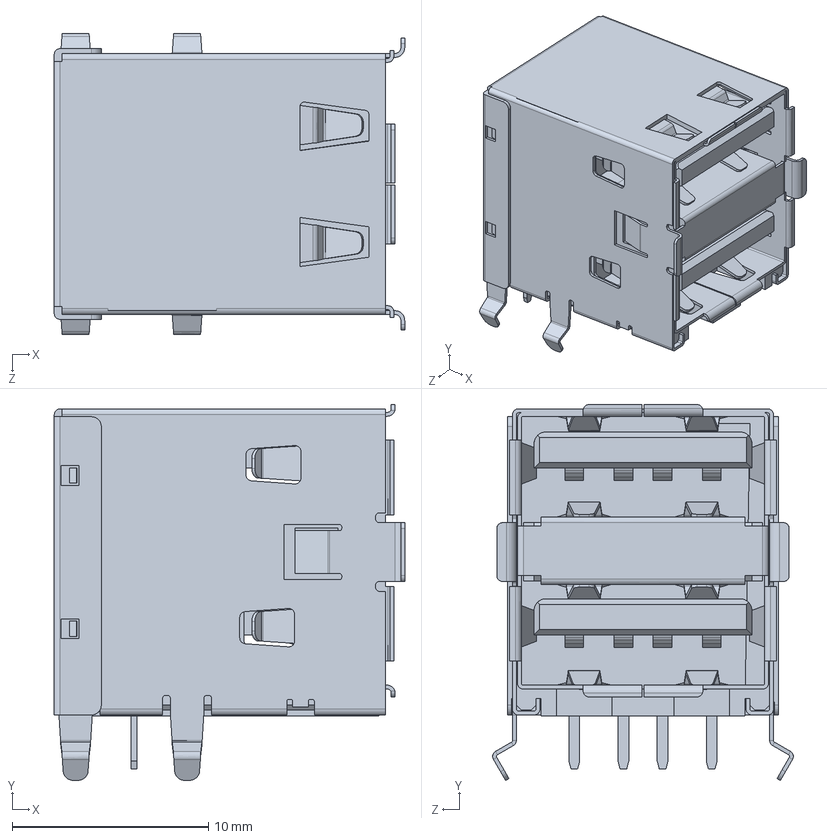
[picture p99: CAD file, 2020-10-01]
RPI4B/BOARD/2X USB2.0 PORTS, RPi4ModelB.SLDPRT
17.9 x 19.2 x 15.3 mm
