mkellsy/rpi-case-model/RPI4B/PUBLISH/BLOWER/BOTTOM.STL

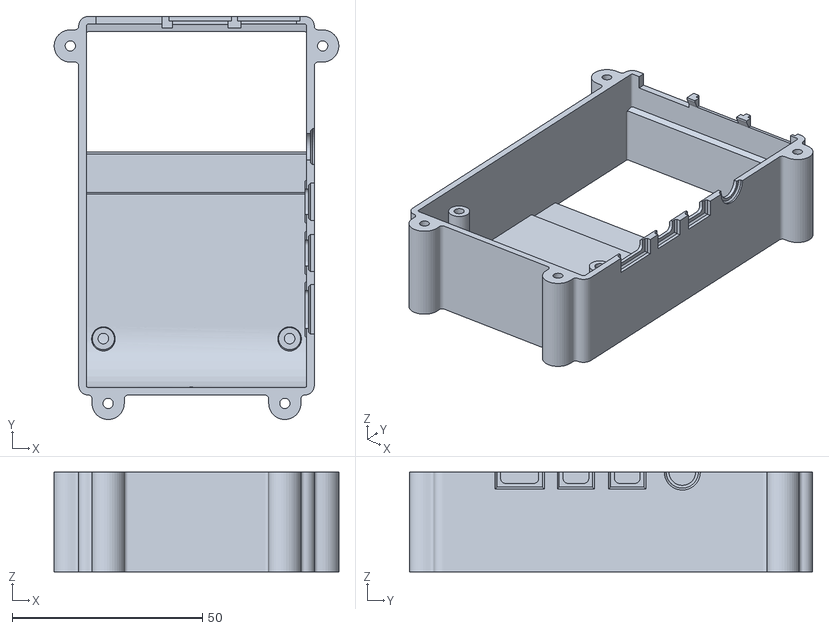
[picture p100: CAD file, 2020-10-01]
RPI4B/PUBLISH/BLOWER/BOTTOM.STL
74.9 x 106.0 x 26.3
