mkellsy/rpi-case-model/RPI4B/PUBLISH/FULL/TOP_SLOTTED.STL

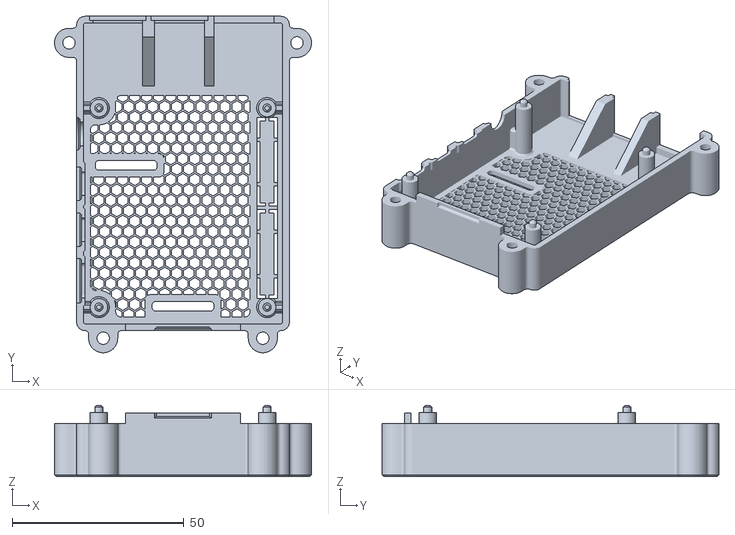
[picture p101: CAD file, 2019-08-11]
RPI4B/PUBLISH/FULL/TOP_SLOTTED.STL
74.9 x 98.0 x 20.7
