mkellsy/rpi-case-model/RPI4B/PUBLISH/GRILL_30MM.STL

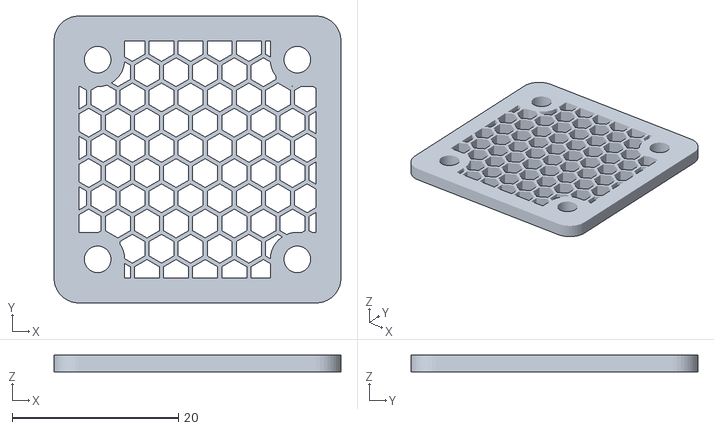
[picture p102: CAD file, 2019-08-16]
RPI4B/PUBLISH/GRILL_30MM.STL
34.5 x 34.5 x 2.00
