mkellsy/rpi-case-model/RPI4B/TOUCHSCREEN/FRAME.SLDPRT

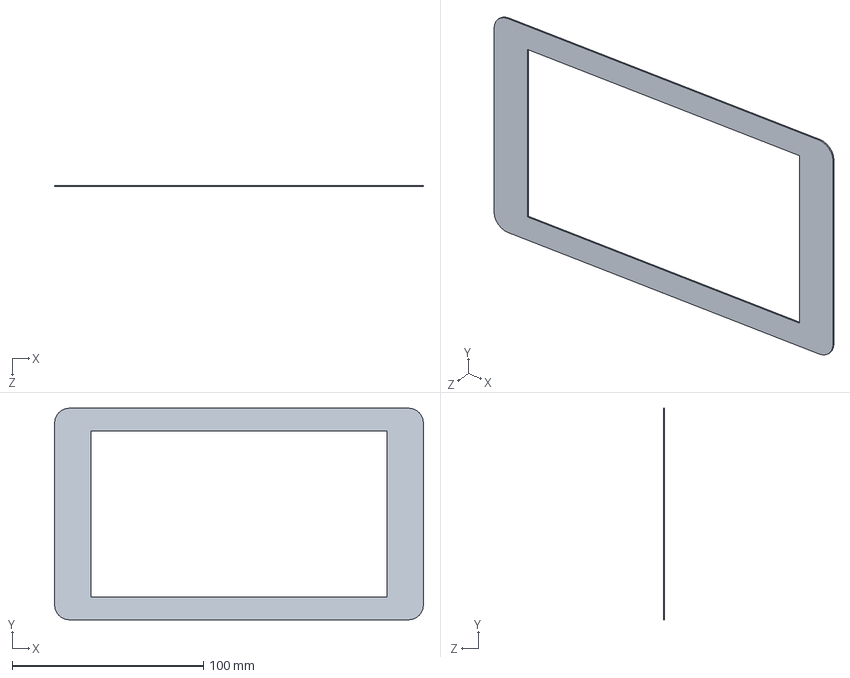
[picture p105: CAD file, 2020-09-30]
RPI4B/TOUCHSCREEN/FRAME.SLDPRT
193.0 x 110.8 x 0.7 mm
