mkellsy/rpi-case-model/RPI3B/BOARD/raspberry_pi_B+_(microsd2).SLDPRT

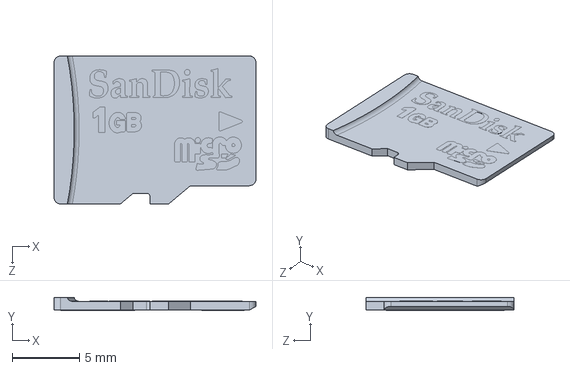
[picture p106: CAD file, 2020-09-30]
RPI3B/BOARD/raspberry_pi_B+_(microsd2).SLDPRT
15.0 x 0.975 x 11.0 mm
