mkellsy/rpi-case-model/RPI3B/CASE/RTS-COVER-40FAN-BLANK.SLDPRT

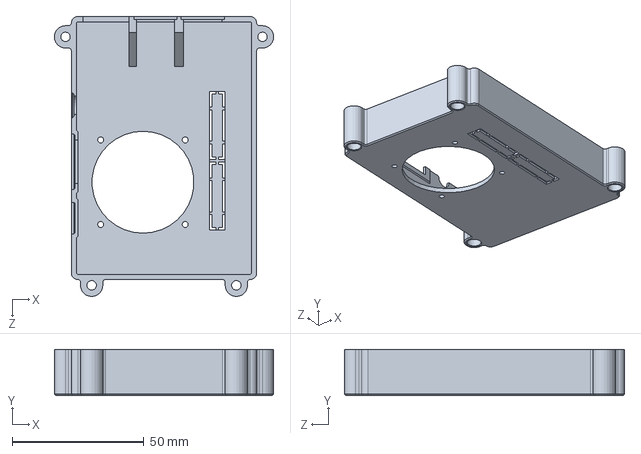
[picture p107: CAD file, 2020-09-30]
RPI3B/CASE/RTS-COVER-40FAN-BLANK.SLDPRT
83.4 x 17.5 x 106.5 mm
