mkellsy/rpi-case-model/RPI4B/BOARD/2X USB3.0 PORTS, RPi4ModelB.SLDPRT

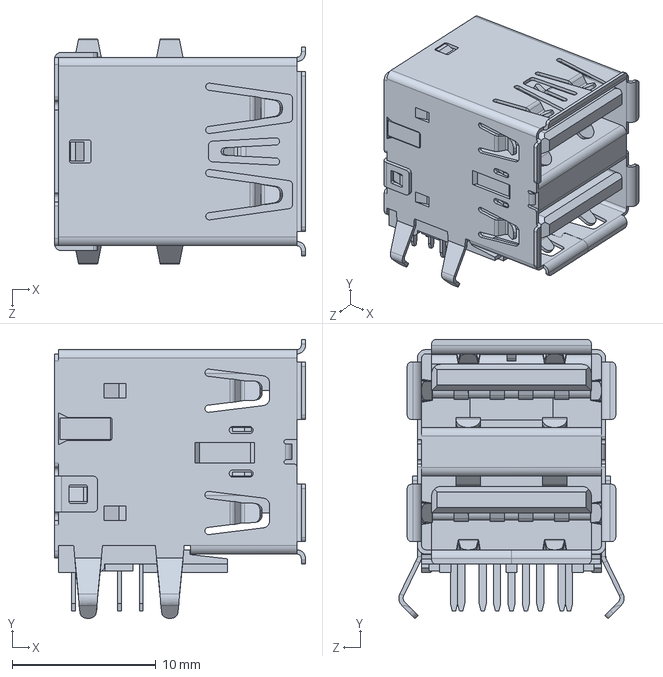
[picture p108: CAD file, 2020-10-01]
RPI4B/BOARD/2X USB3.0 PORTS, RPi4ModelB.SLDPRT
17.5 x 19.4 x 15.7 mm
