mkellsy/rpi-case-model/RPI4B/CASE/RIGHT-LEG.SLDPRT

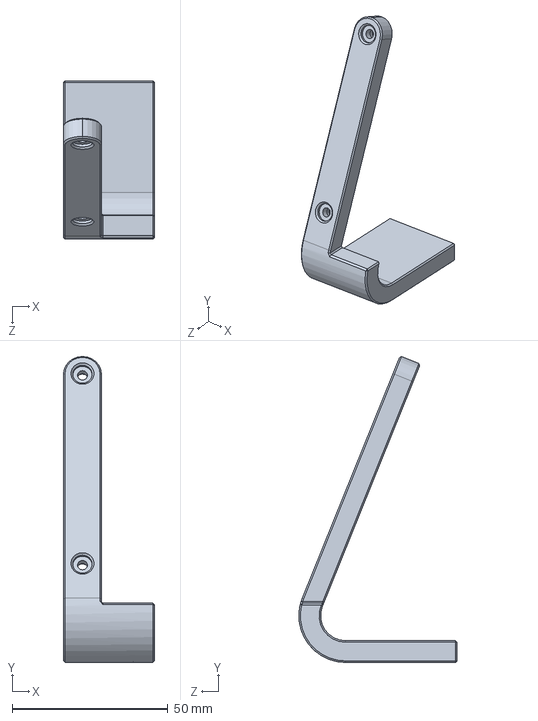
[picture p109: CAD file, 2020-09-30]
RPI4B/CASE/RIGHT-LEG.SLDPRT
29.2 x 98.1 x 50.8 mm
