mkellsy/rpi-case-model/RPI4B/COMPONENTS/BLADES.SLDPRT

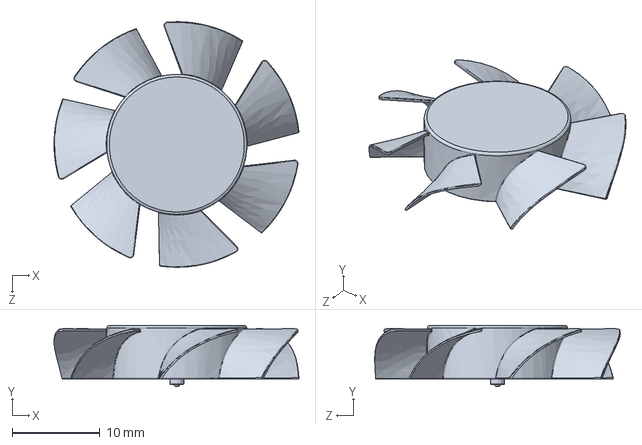
[picture p110: CAD file, 2020-10-01]
RPI4B/COMPONENTS/BLADES.SLDPRT
27.9 x 7.00 x 28.0 mm
