mkellsy/rpi-case-model/RPI4B/PUBLISH/BLOWER/TOP-VENTED.STL

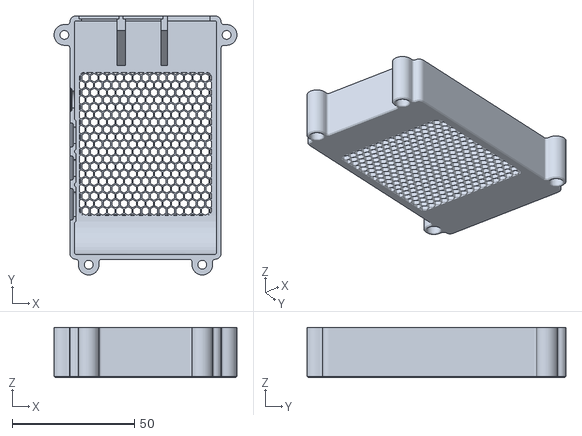
[picture p111: CAD file, 2020-10-01]
RPI4B/PUBLISH/BLOWER/TOP-VENTED.STL
74.9 x 106.0 x 20.5
