mkellsy/rpi-case-model/RPI4B/PUBLISH/FULL/TOP_25MM_SLOTTED.STL

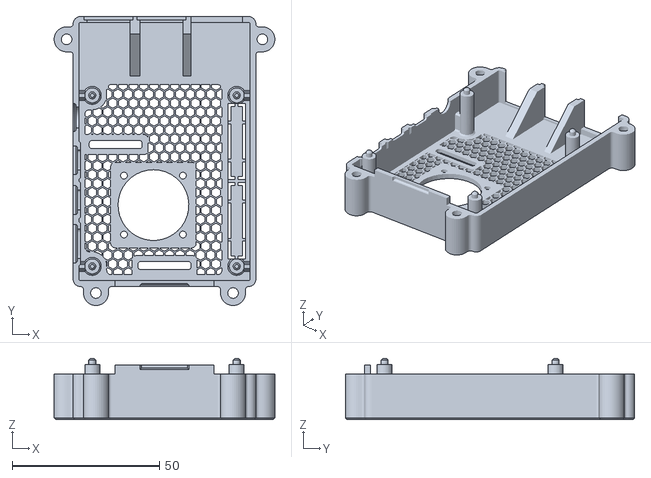
[picture p112: CAD file, 2019-08-11]
RPI4B/PUBLISH/FULL/TOP_25MM_SLOTTED.STL
74.9 x 98.0 x 20.7
