mkellsy/rpi-case-model/RPI4B/PUBLISH/GRILL_25MM.STL

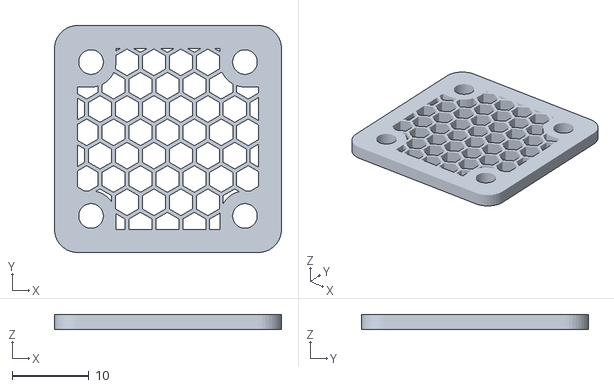
[picture p113: CAD file, 2019-08-16]
RPI4B/PUBLISH/GRILL_25MM.STL
29.5 x 29.5 x 2.00
