mkellsy/rpi-case-model/RPI4B/TOUCHSCREEN/HOUSING.SLDPRT

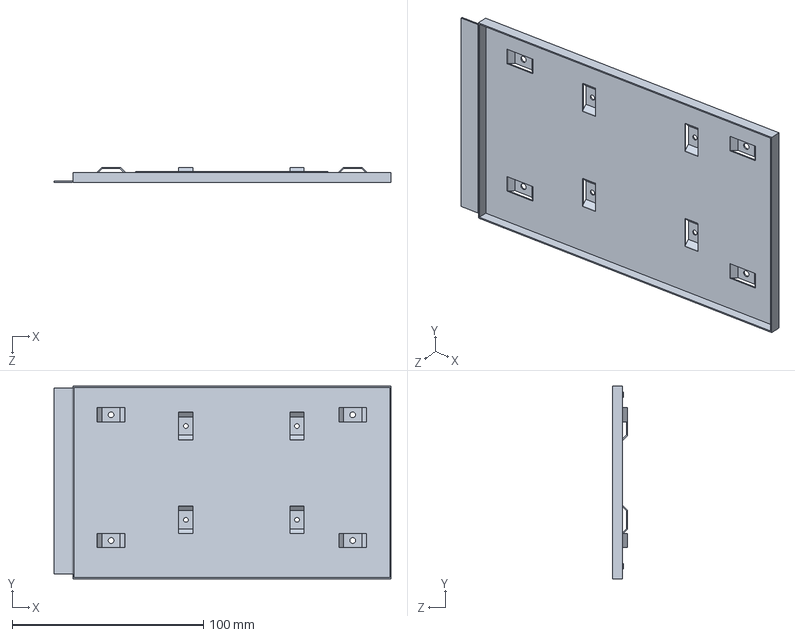
[picture p117: CAD file, 2020-09-30]
RPI4B/TOUCHSCREEN/HOUSING.SLDPRT
176.0 x 100.6 x 7.76 mm
