mkellsy/rpi-case-model/RPI3B/CASE/RTS-COVER-40FAN.SLDPRT

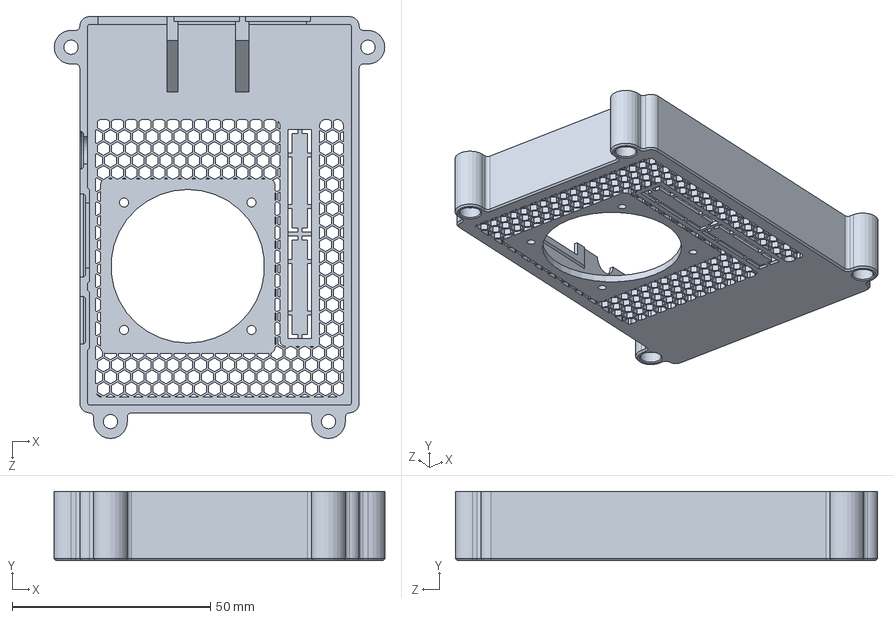
[picture p118: CAD file, 2020-09-30]
RPI3B/CASE/RTS-COVER-40FAN.SLDPRT
83.4 x 17.5 x 106.5 mm
