mkellsy/rpi-case-model/RPI4B/BLOWER/MMDVM.SLDPRT

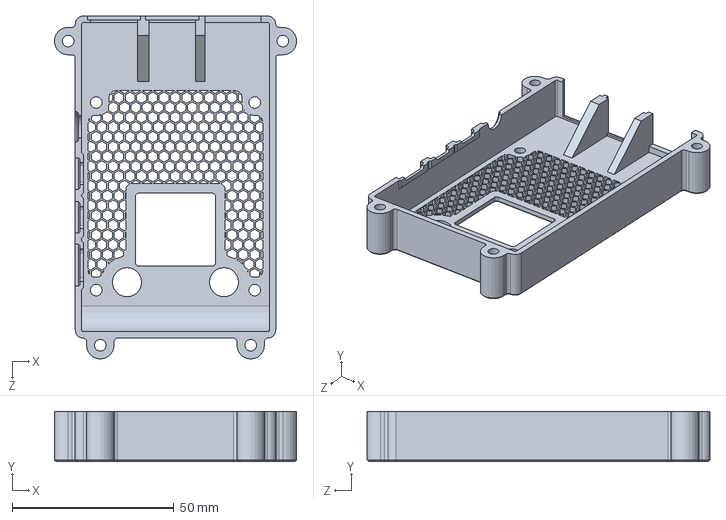
[picture p119: CAD file, 2020-10-01]
RPI4B/BLOWER/MMDVM.SLDPRT
74.9 x 15.5 x 106.1 mm
