mkellsy/rpi-case-model/RPI4B/BOARD/PCB, RPi4ModelB.SLDPRT

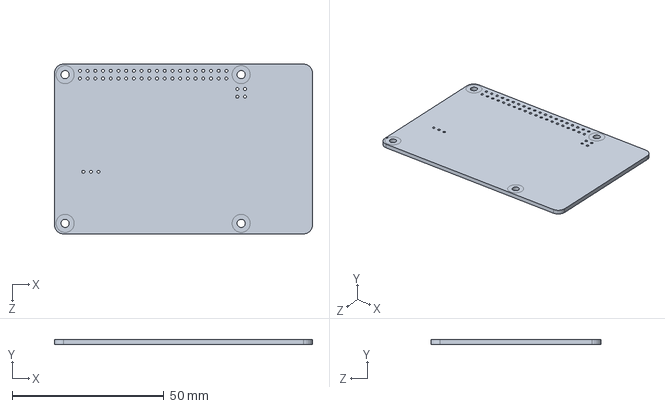
[picture p120: CAD file, 2020-09-30]
RPI4B/BOARD/PCB, RPi4ModelB.SLDPRT
85.0 x 1.60 x 56.0 mm
