mkellsy/rpi-case-model/RPI4B/COMPONENTS/FAN_25MM.SLDPRT

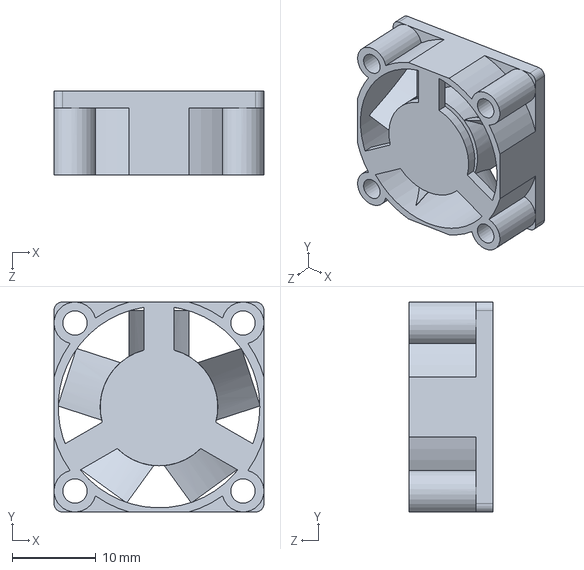
[picture p121: CAD file, 2020-09-30]
RPI4B/COMPONENTS/FAN_25MM.SLDPRT
25.0 x 25.0 x 10.0 mm
