mkellsy/rpi-case-model/RPI4B/PUBLISH/BLOWER/BASE.STL

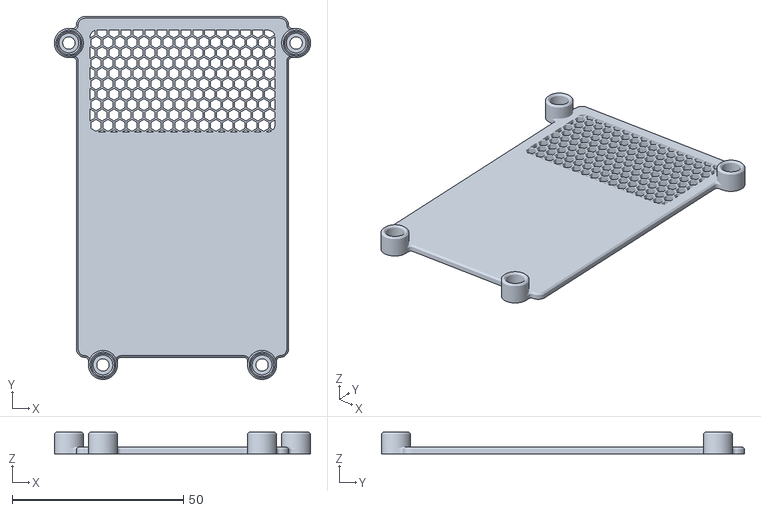
[picture p122: CAD file, 2020-10-01]
RPI4B/PUBLISH/BLOWER/BASE.STL
74.9 x 106.0 x 6.40
