mkellsy/rpi-case-model/RPI4B/PUBLISH/TOUCHSCREEN/TOP_25MM.STL

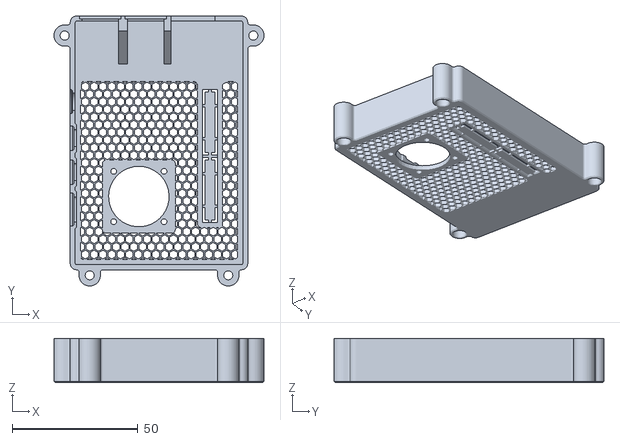
[picture p124: CAD file, 2020-09-30]
RPI4B/PUBLISH/TOUCHSCREEN/TOP_25MM.STL
83.4 x 107.2 x 17.5
