mkellsy/rpi-case-model/RPI4B/TOUCHSCREEN/RAISER.SLDPRT

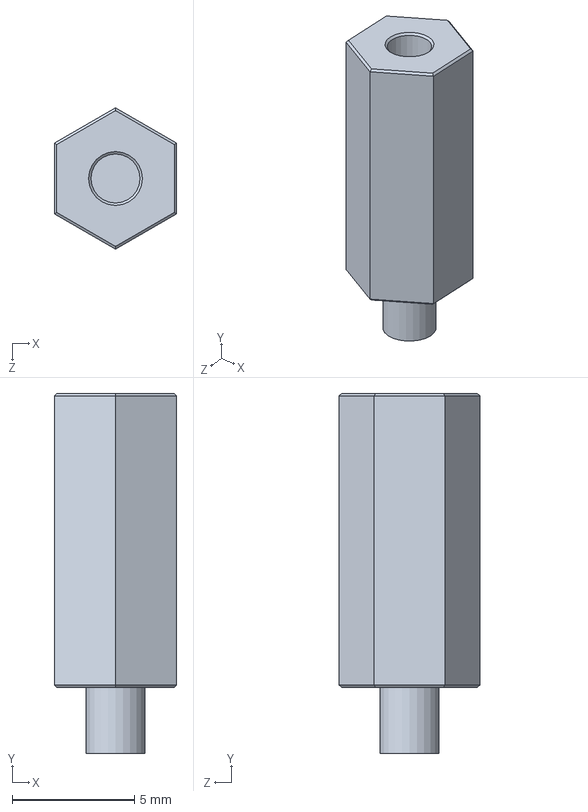
[picture p125: CAD file, 2020-09-30]
RPI4B/TOUCHSCREEN/RAISER.SLDPRT
5.00 x 14.7 x 5.77 mm
