mkellsy/rpi-case-model/RPI3B/CASE/RTS-COVER-30FAN-BLANK.SLDPRT

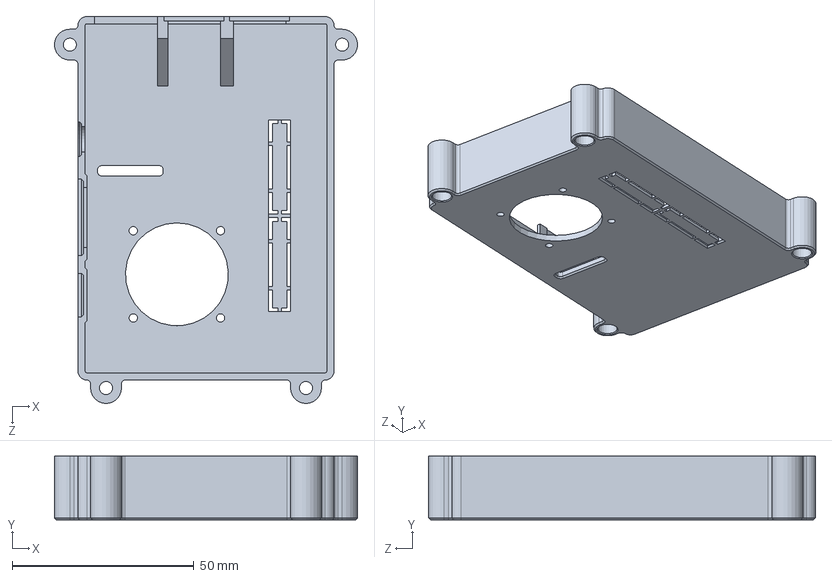
[picture p126: CAD file, 2020-09-30]
RPI3B/CASE/RTS-COVER-30FAN-BLANK.SLDPRT
83.4 x 17.5 x 106.5 mm
