mkellsy/rpi-case-model/RPI3B/PUBLISH/RTS-TEMPLATE.STL

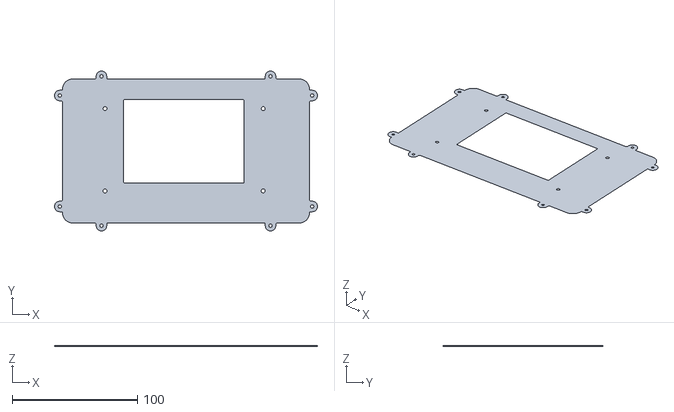
[picture p127: CAD file, 2019-08-06]
RPI3B/PUBLISH/RTS-TEMPLATE.STL
209.8 x 127.6 x 0.4
