mkellsy/rpi-case-model/RPI4B/BOARD/Cypress CYW43455 Wireless Module Cover, RPi4ModelB.SLDPRT

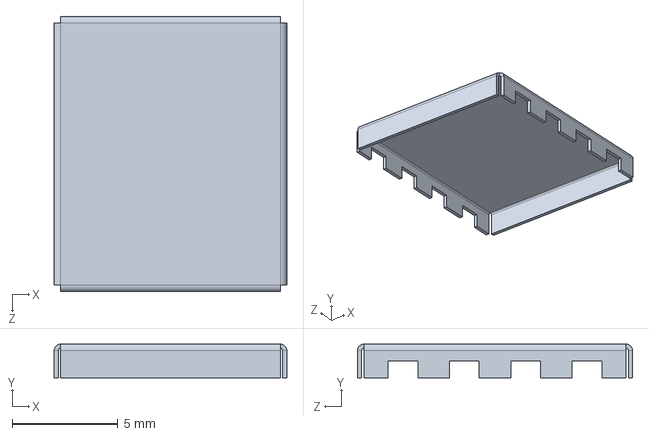
[picture p128: CAD file, 2020-09-30]
RPI4B/BOARD/Cypress CYW43455 Wireless Module Cover, RPi4ModelB.SLDPRT
11.0 x 1.60 x 13.0 mm
