mkellsy/rpi-case-model/RPI4B/CASE/GRILL_25MM.SLDPRT

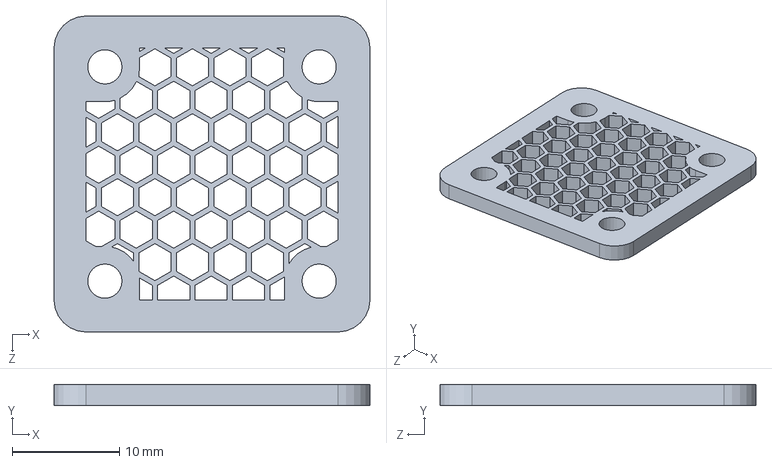
[picture p129: CAD file, 2020-09-30]
RPI4B/CASE/GRILL_25MM.SLDPRT
29.5 x 2.00 x 29.5 mm
