mkellsy/rpi-case-model/RPI4B/COMPONENTS/FAN_30MM.SLDPRT

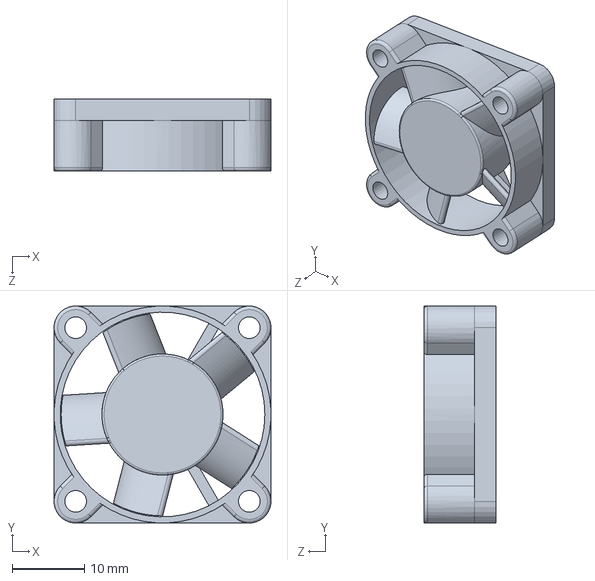
[picture p130: CAD file, 2020-09-30]
RPI4B/COMPONENTS/FAN_30MM.SLDPRT
30.0 x 30.0 x 10.0 mm
