mkellsy/rpi-case-model/RPI4B/PUBLISH/STANDARD/TOP_25MM_BLANK.STL

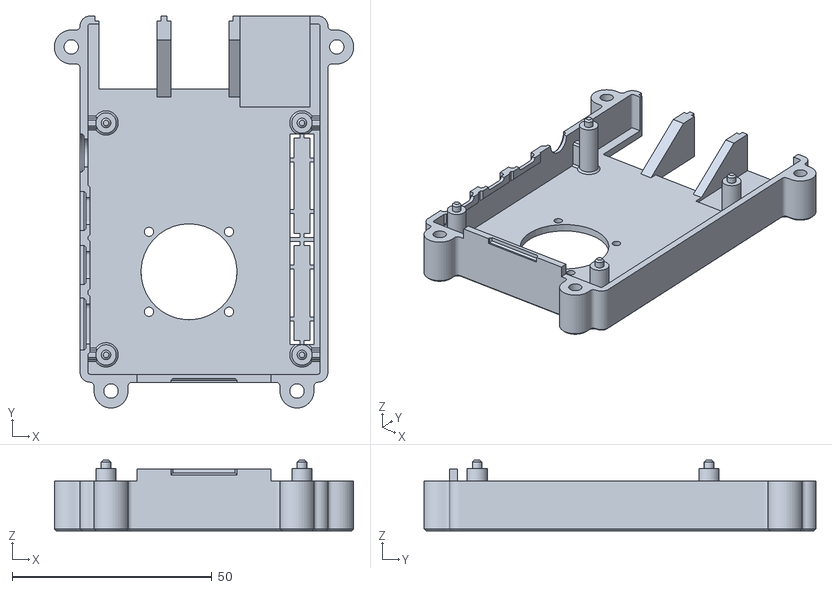
[picture p131: CAD file, 2019-08-11]
RPI4B/PUBLISH/STANDARD/TOP_25MM_BLANK.STL
74.9 x 98.0 x 17.7
