mkellsy/rpi-case-model/RPI4B/TOUCHSCREEN/DRIVER-BOARD.SLDPRT

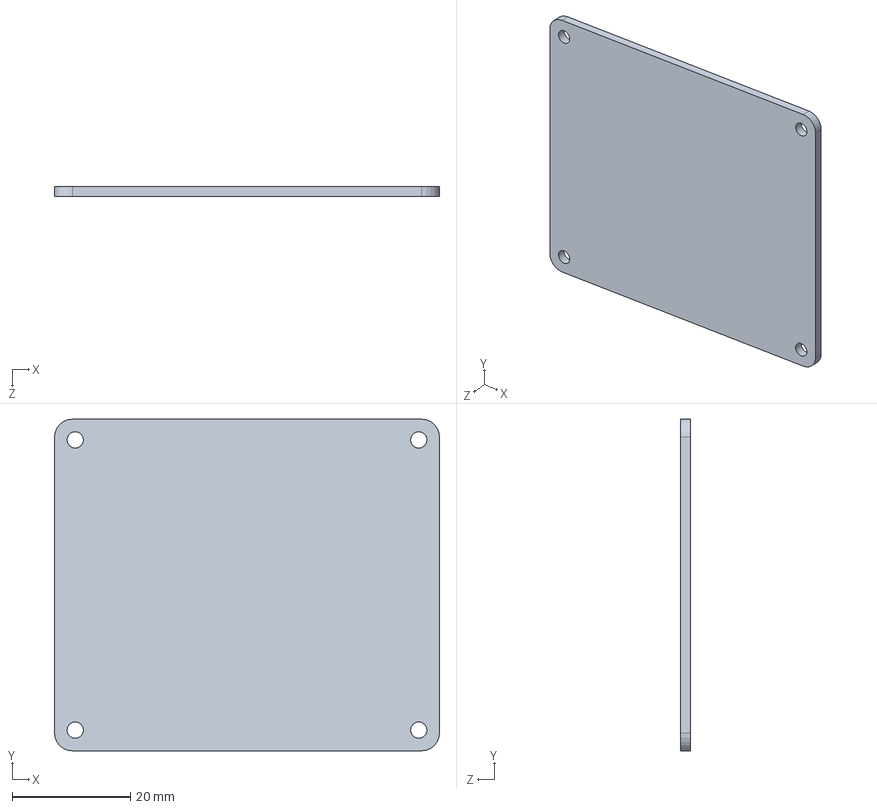
[picture p132: CAD file, 2020-09-30]
RPI4B/TOUCHSCREEN/DRIVER-BOARD.SLDPRT
65.0 x 56.0 x 1.75 mm
