mkellsy/rpi-case-model/RPI3B/CASE/RPI-BOTTOM-100VESA.SLDPRT

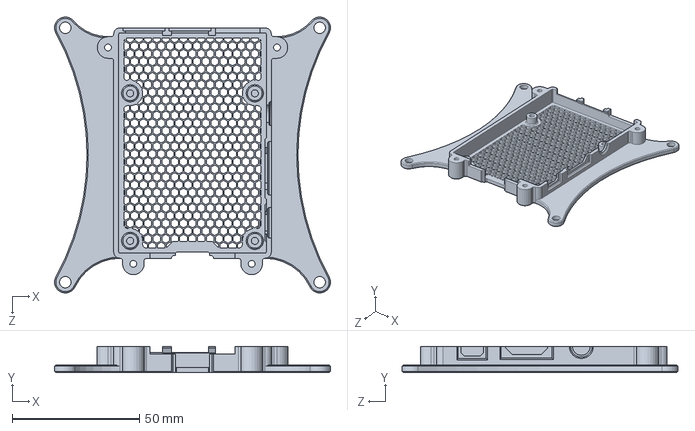
[picture p133: CAD file, 2020-09-30]
RPI3B/CASE/RPI-BOTTOM-100VESA.SLDPRT
108.5 x 10.3 x 108.5 mm
