mkellsy/rpi-case-model/RPI4B/BOARD/Broadcom BCM54213PE Gigabit Ethernet Transceiver, RPi4ModelB.SLDPRT

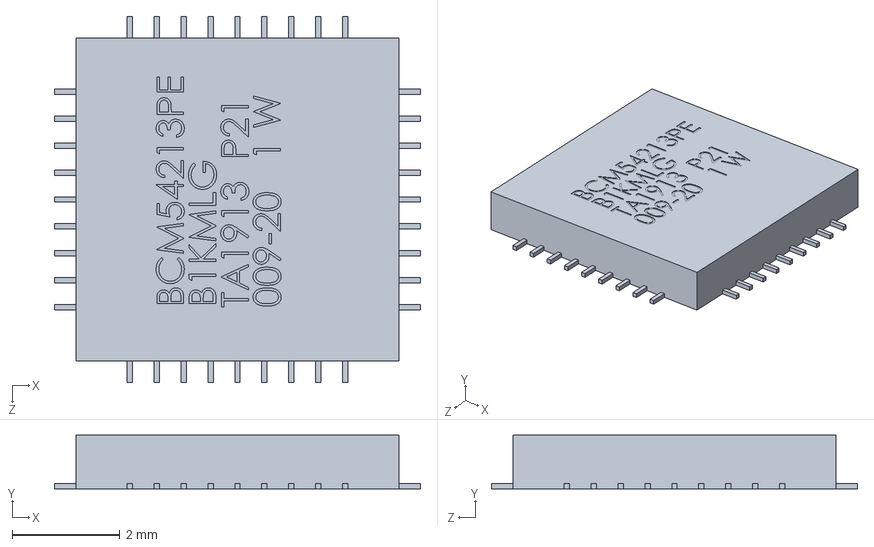
[picture p134: CAD file, 2020-09-30]
RPI4B/BOARD/Broadcom BCM54213PE Gigabit Ethernet Transceiver, RPi4ModelB.SLDPRT
6.80 x 1.00 x 6.80 mm
