mkellsy/rpi-case-model/RPI4B/COMPONENTS/FAN_40MM.SLDPRT

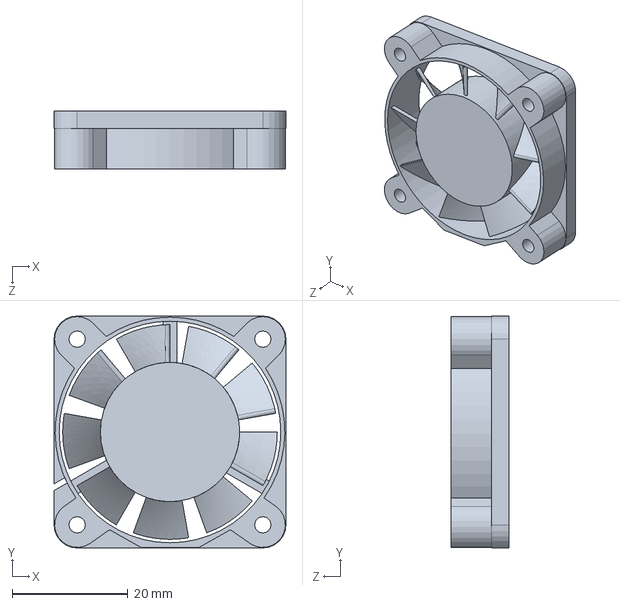
[picture p135: CAD file, 2020-09-30]
RPI4B/COMPONENTS/FAN_40MM.SLDPRT
40.0 x 40.0 x 10.0 mm
