mkellsy/rpi-case-model/RPI3B/BOARD/molex_0473460001.sldprt

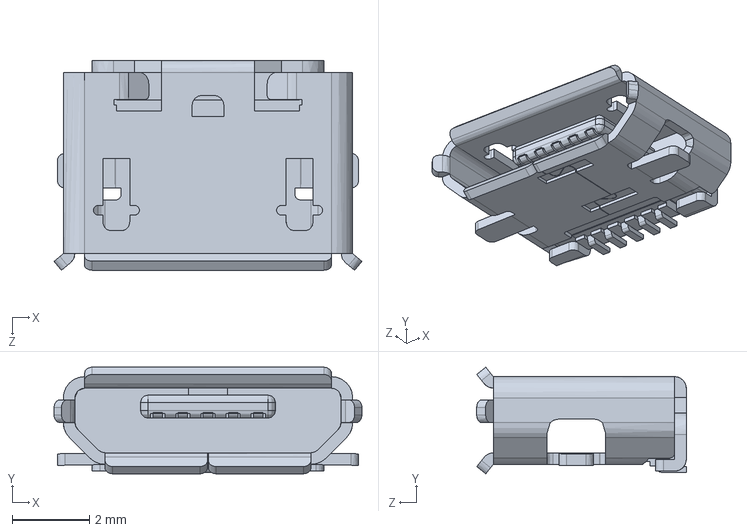
[picture p137: CAD file, 2020-09-30]
RPI3B/BOARD/molex_0473460001.sldprt
7.98 x 2.76 x 5.43 mm
