mkellsy/rpi-case-model/RPI4B/BOARD/Female USB Type C Connector, RPi4ModelB.SLDPRT

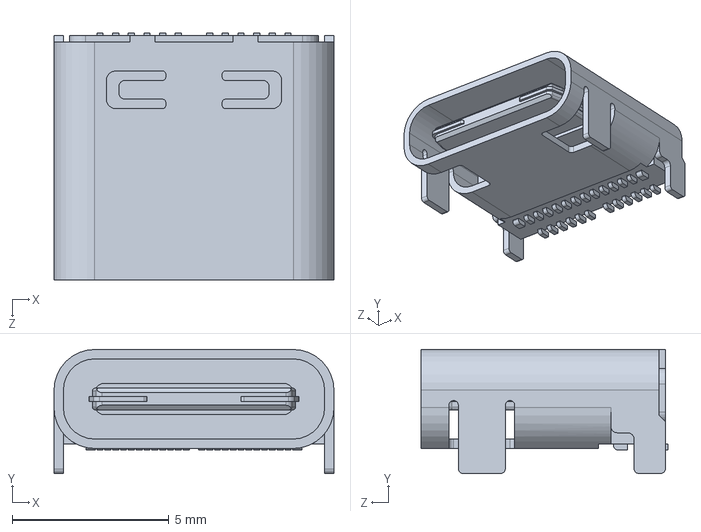
[picture p138: CAD file, 2020-09-30]
RPI4B/BOARD/Female USB Type C Connector, RPi4ModelB.SLDPRT
8.94 x 3.96 x 7.90 mm
