mkellsy/rpi-case-model/RPI4B/CASE/GRILL_40MM.SLDPRT

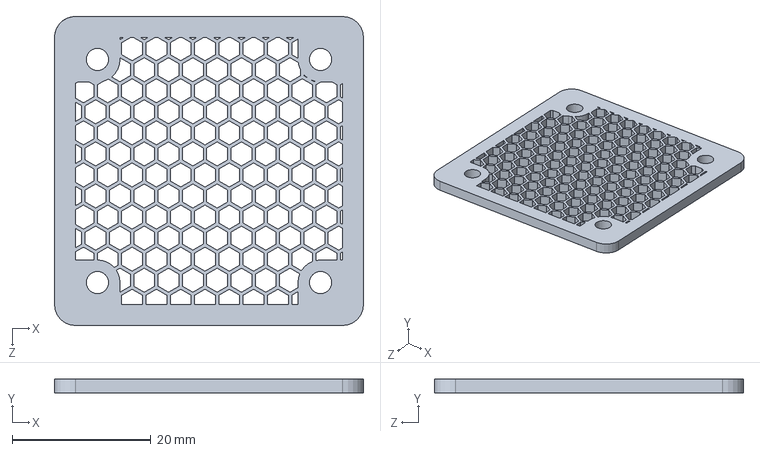
[picture p139: CAD file, 2020-09-30]
RPI4B/CASE/GRILL_40MM.SLDPRT
44.5 x 2.00 x 44.5 mm
