mkellsy/rpi-case-model/RPI4B/BOARD/SD Card Slot, RPi4ModelB.SLDPRT

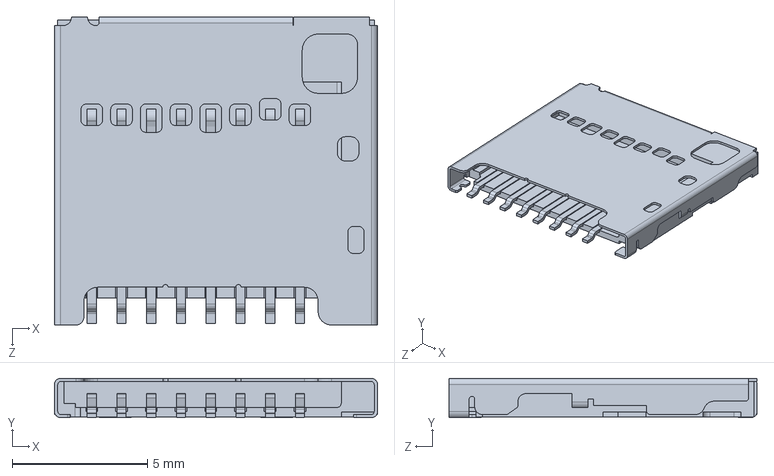
[picture p142: CAD file, 2020-09-30]
RPI4B/BOARD/SD Card Slot, RPi4ModelB.SLDPRT
11.9 x 1.45 x 11.4 mm
