mkellsy/rpi-case-model/RPI4B/CASE/BOTTOM.SLDPRT

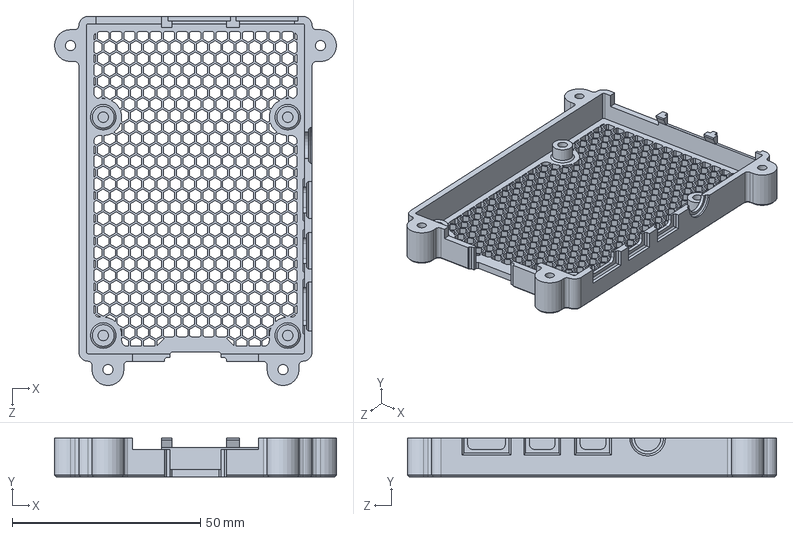
[picture p143: CAD file, 2019-08-06]
RPI4B/CASE/BOTTOM.SLDPRT
74.9 x 10.3 x 98.1 mm
