mkellsy/rpi-case-model/RPI3B/BOARD/molex_0471510001.sldprt

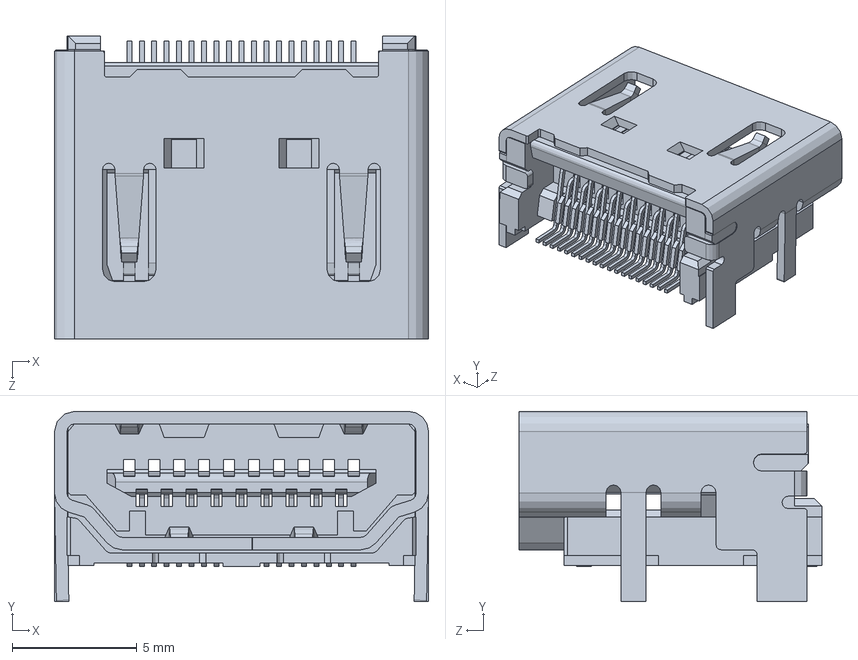
[picture p144: CAD file, 2020-09-30]
RPI3B/BOARD/molex_0471510001.sldprt
15.0 x 7.63 x 12.1 mm
