mkellsy/rpi-case-model/RPI3B/CASE/RPI-TOP-SLOTTED.SLDPRT

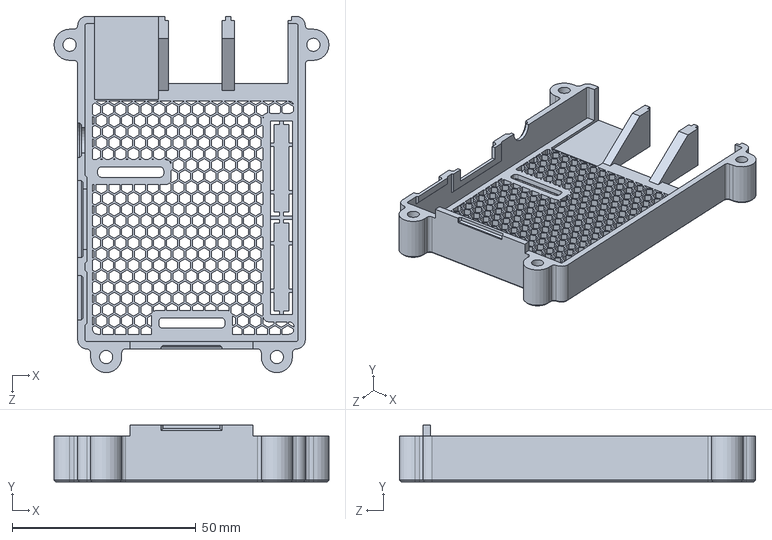
[picture p145: CAD file, 2020-09-30]
RPI3B/CASE/RPI-TOP-SLOTTED.SLDPRT
74.9 x 15.5 x 97.0 mm
