mkellsy/rpi-case-model/RPI3B/PUBLISH/RPI-TOP-25FAN-BLANK.STL

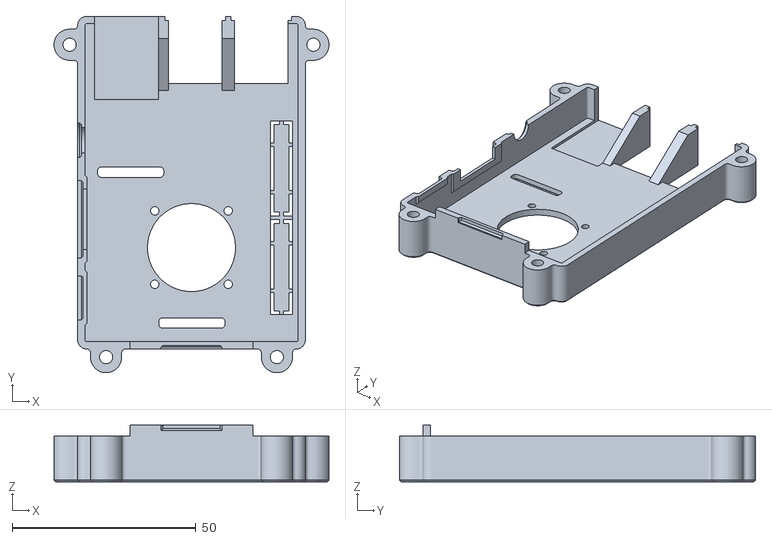
[picture p146: CAD file, 2019-01-22]
RPI3B/PUBLISH/RPI-TOP-25FAN-BLANK.STL
74.9 x 97.0 x 15.5
