mkellsy/rpi-case-model/RPI4B/BOARD/MxL7704 Universal PMIC, RPi4ModelB.SLDPRT

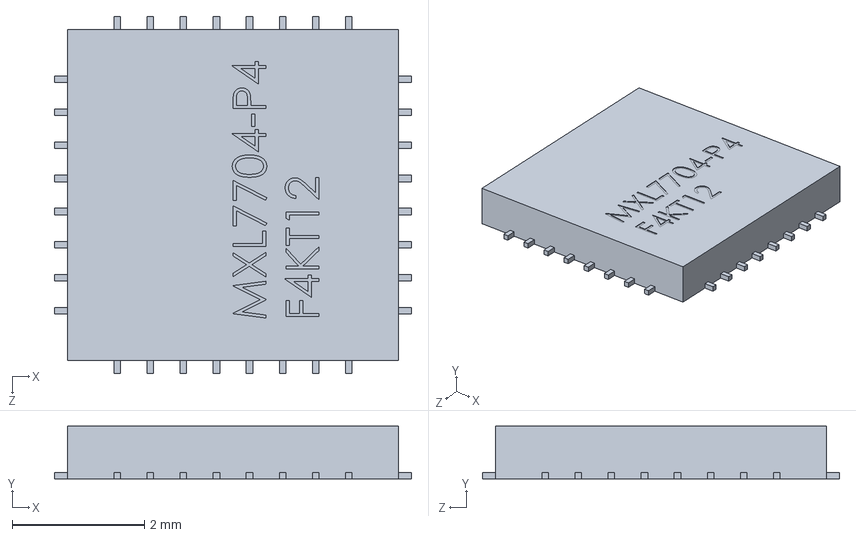
[picture p147: CAD file, 2020-09-30]
RPI4B/BOARD/MxL7704 Universal PMIC, RPi4ModelB.SLDPRT
5.40 x 0.8 x 5.40 mm
