mkellsy/rpi-case-model/RPI3B/BOARD/raspberry_pi_3(bar_180_2x20).SLDPRT

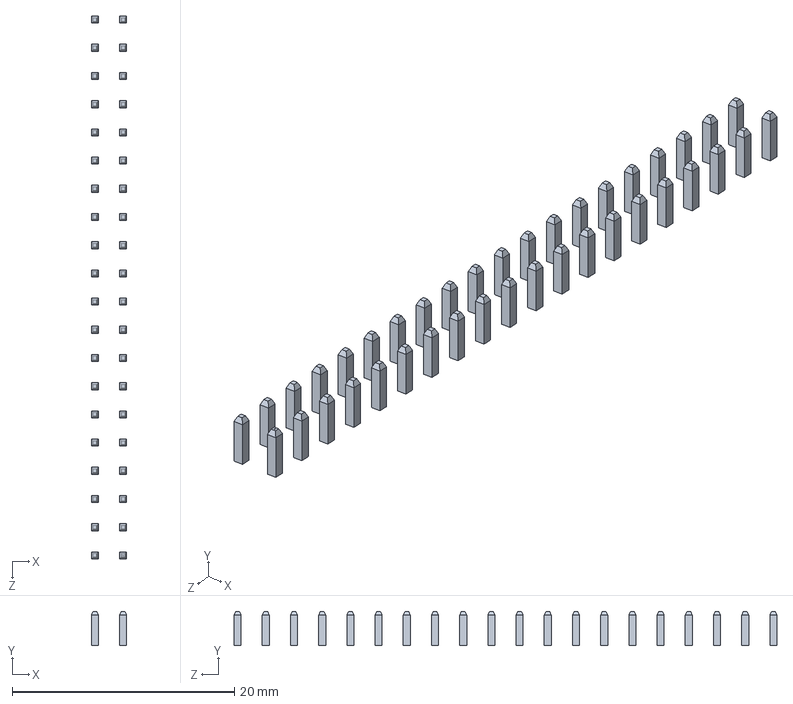
[picture p148: CAD file, 2020-09-30]
RPI3B/BOARD/raspberry_pi_3(bar_180_2x20).SLDPRT
3.19 x 3.10 x 48.9 mm
