mkellsy/rpi-case-model/RPI3B/CASE/RPI-BOTTOM-75VESA.SLDPRT

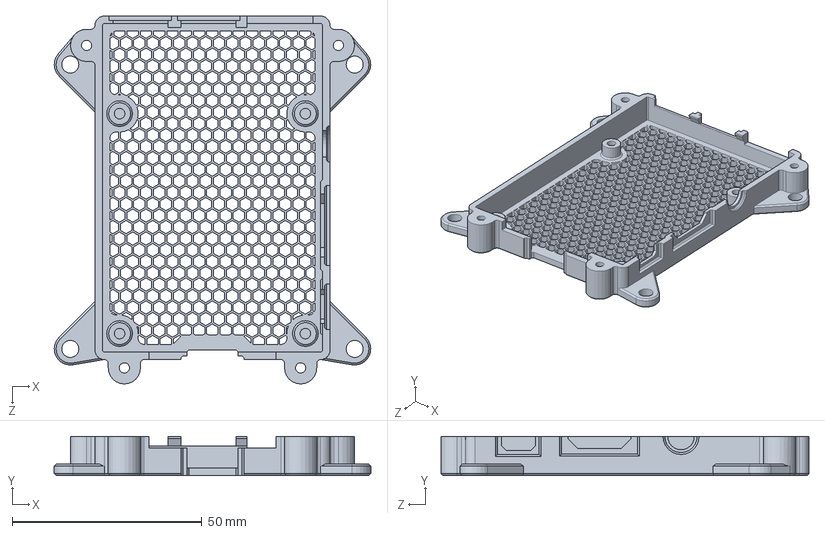
[picture p149: CAD file, 2020-09-30]
RPI3B/CASE/RPI-BOTTOM-75VESA.SLDPRT
83.5 x 10.3 x 97.0 mm
