mkellsy/rpi-case-model/RPI4B/BOARD/Female Micro HDMI Connector, RPi4ModelB.SLDPRT

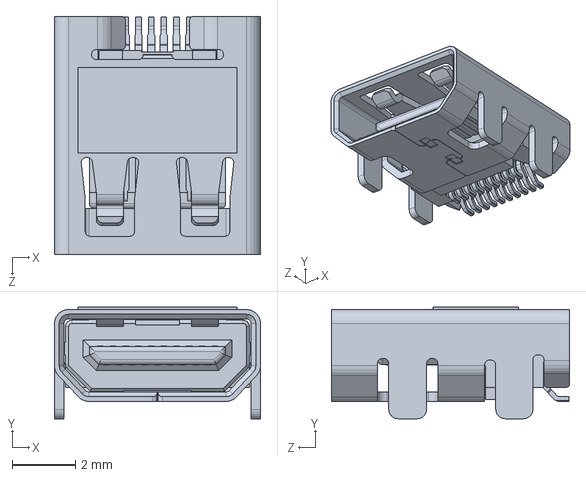
[picture p150: CAD file, 2020-09-30]
RPI4B/BOARD/Female Micro HDMI Connector, RPi4ModelB.SLDPRT
6.50 x 3.52 x 7.50 mm
