mkellsy/rpi-case-model/RPI4B/PUBLISH/SLIM/TOP.STL

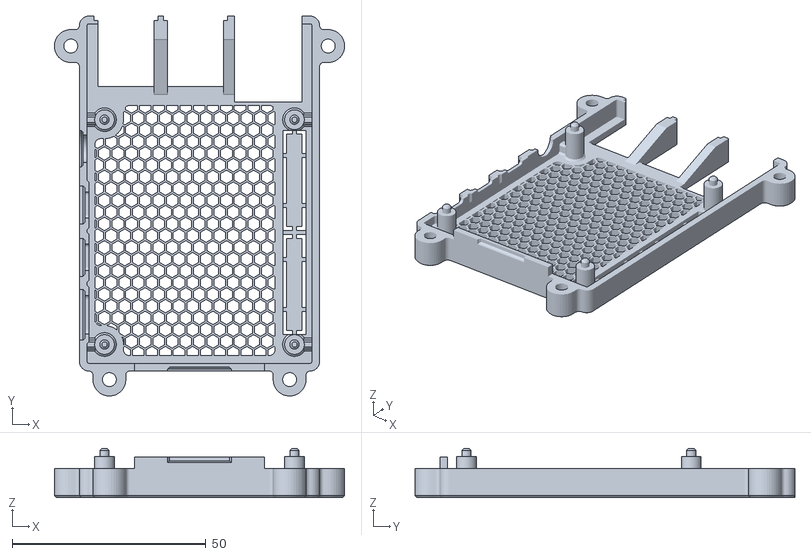
[picture p151: CAD file, 2019-08-11]
RPI4B/PUBLISH/SLIM/TOP.STL
74.9 x 98.0 x 12.7
