mkellsy/rpi-case-model/RPI3B/CASE/RPI-BOTTOM-8020.SLDPRT

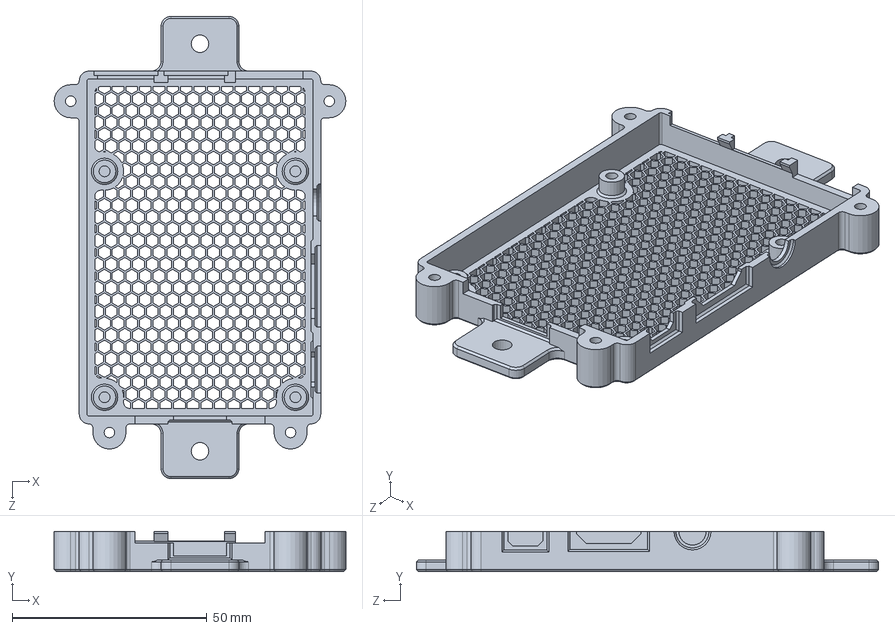
[picture p152: CAD file, 2020-09-30]
RPI3B/CASE/RPI-BOTTOM-8020.SLDPRT
74.9 x 10.3 x 118.6 mm
