mkellsy/rpi-case-model/RPI3B/PUBLISH/RPI-TOP-SLOTTED-BLANK.STL

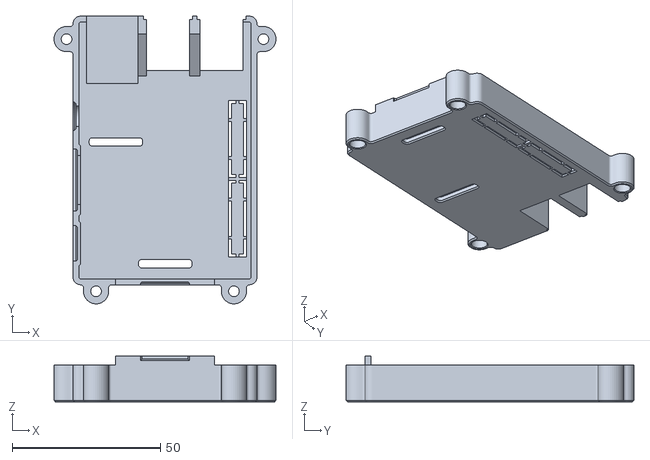
[picture p153: CAD file, 2019-01-22]
RPI3B/PUBLISH/RPI-TOP-SLOTTED-BLANK.STL
74.9 x 97.0 x 15.5
