mkellsy/rpi-case-model/RPI4B/BOARD/Camera Connector, RPi4ModelB.SLDPRT

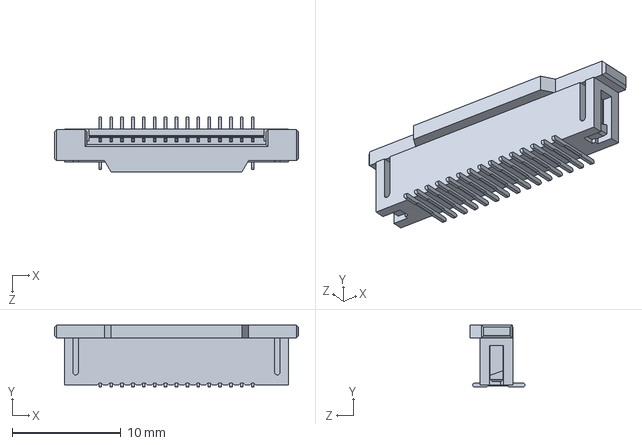
[picture p154: CAD file, 2020-09-30]
RPI4B/BOARD/Camera Connector, RPi4ModelB.SLDPRT
22.4 x 5.68 x 5.07 mm
