mkellsy/rpi-case-model/RPI4B/BOARD/Microphone Plug, RPi4ModelB.SLDPRT

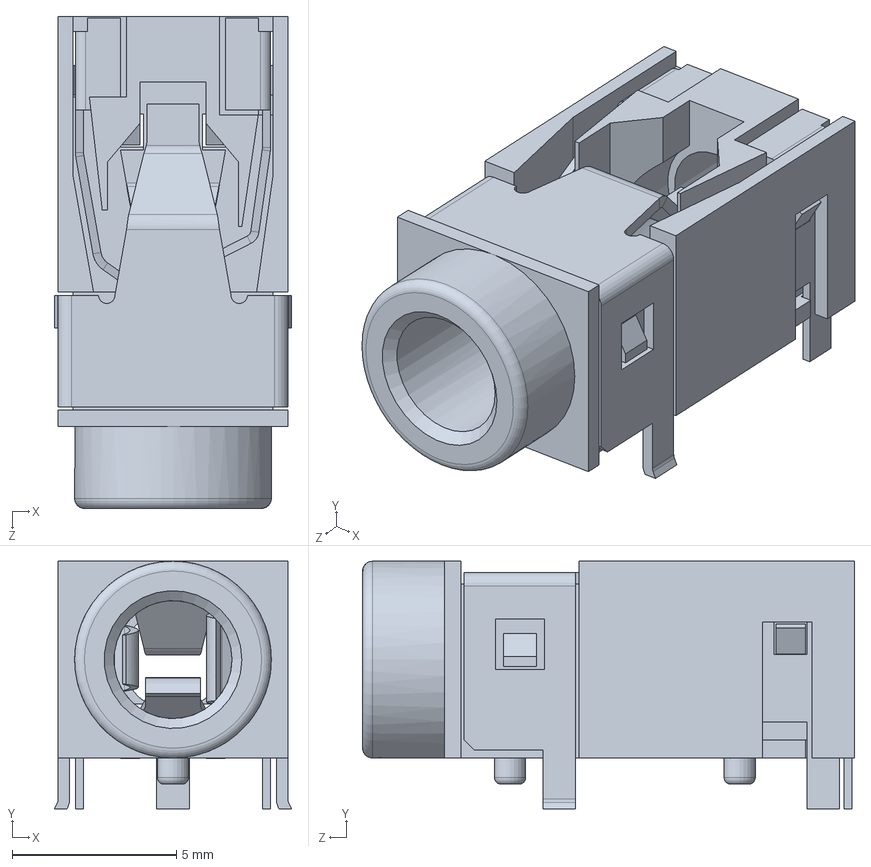
[picture p156: CAD file, 2020-09-30]
RPI4B/BOARD/Microphone Plug, RPi4ModelB.SLDPRT
7.23 x 7.55 x 15.0 mm
