mkellsy/rpi-case-model/RPI3B/BOARD/Raspberry Pi 31.sldprt

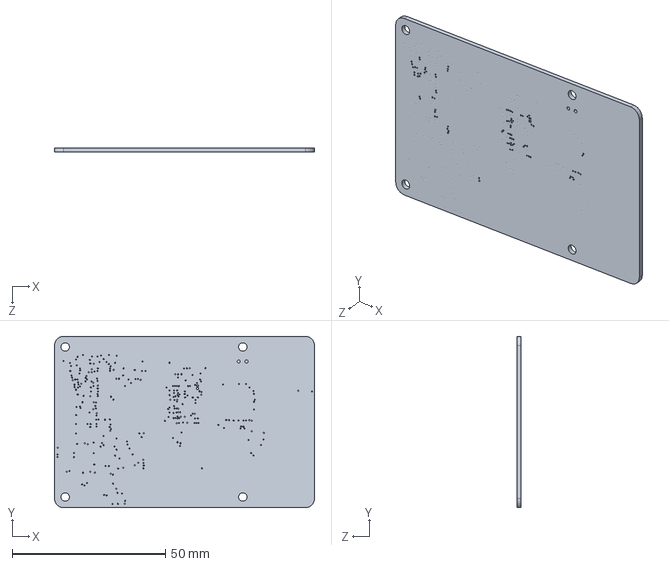
[picture p157: CAD file, 2020-09-30]
RPI3B/BOARD/Raspberry Pi 31.sldprt
84.9 x 56.0 x 1.33 mm
