mkellsy/rpi-case-model/RPI3B/PUBLISH/RPI-TOP-25FAN.STL

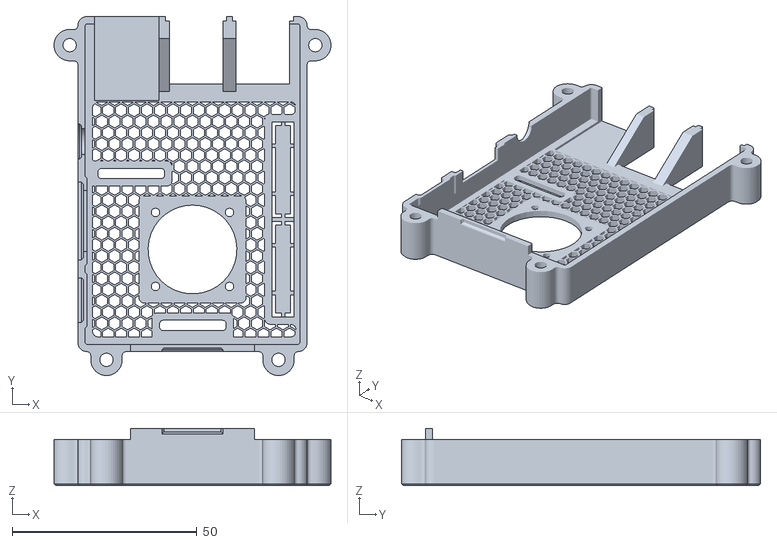
[picture p158: CAD file, 2019-01-20]
RPI3B/PUBLISH/RPI-TOP-25FAN.STL
74.9 x 97.0 x 15.5
