mkellsy/rpi-case-model/RPI3B/BOARD/raspberry_pi_B_(RJ45).SLDPRT

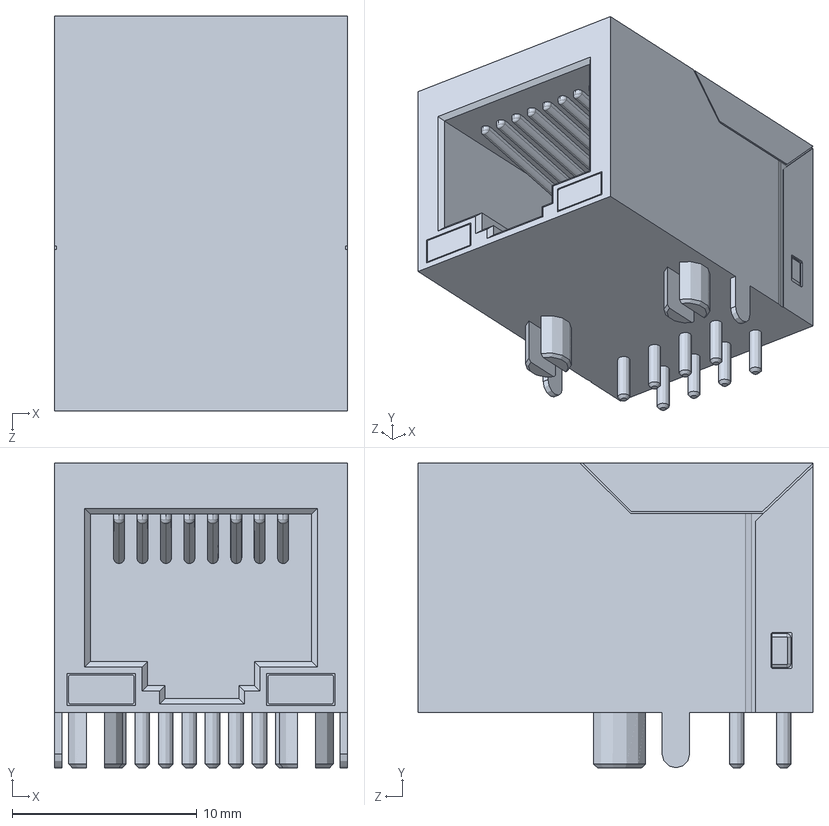
[picture p159: CAD file, 2020-09-30]
RPI3B/BOARD/raspberry_pi_B_(RJ45).SLDPRT
15.9 x 16.5 x 21.4 mm
