mkellsy/rpi-case-model/RPI4B/BOARD/VIA VL805 PCIe USB 3.0 controller, RPi4ModelB.SLDPRT

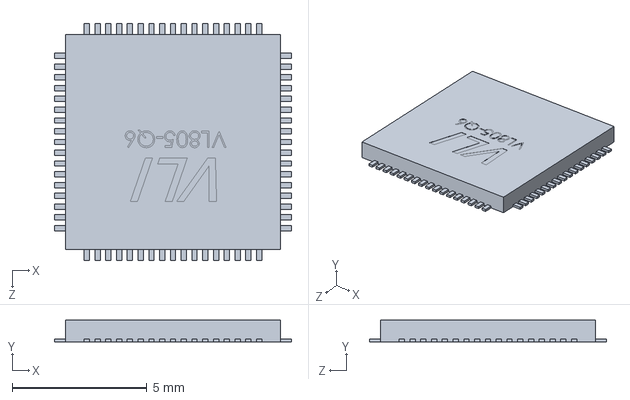
[picture p160: CAD file, 2020-09-30]
RPI4B/BOARD/VIA VL805 PCIe USB 3.0 controller, RPi4ModelB.SLDPRT
8.80 x 0.8 x 8.80 mm
